RBinsonB/Nox_robot/CAD/Solidworks/Kinect support/wood_planck_kinect.SLDPRT

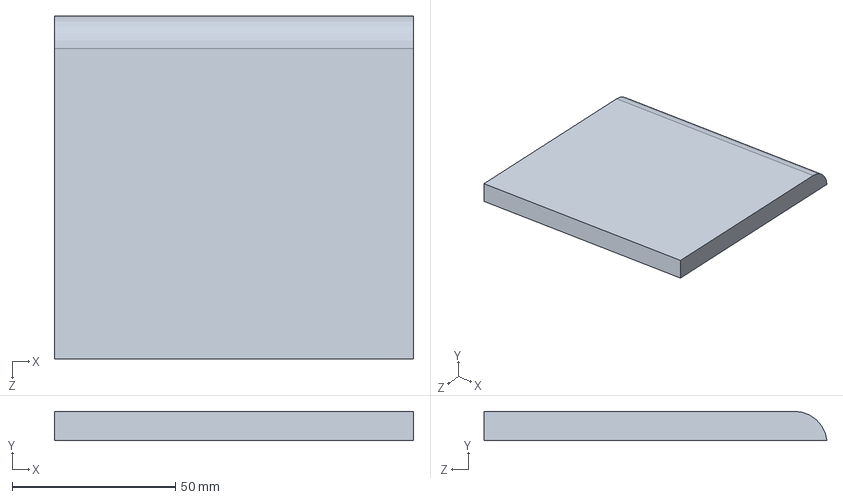
[picture p22: CAD file, 2019-08-14]
CAD/Solidworks/Kinect support/wood_planck_kinect.SLDPRT
110.0 x 9.00 x 105.0 mm
