RBinsonB/Nox_robot/CAD/Solidworks/Motor/Attache_moteur.SLDPRT

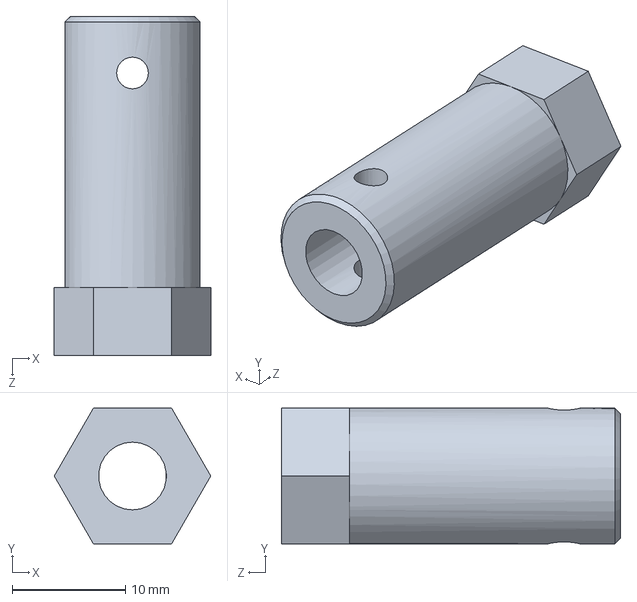
[picture p23: CAD file, 2019-08-14]
CAD/Solidworks/Motor/Attache_moteur.SLDPRT
13.9 x 12.0 x 30.0 mm
