RBinsonB/Nox_robot/CAD/Solidworks/Pivoting roller/Roller.SLDPRT

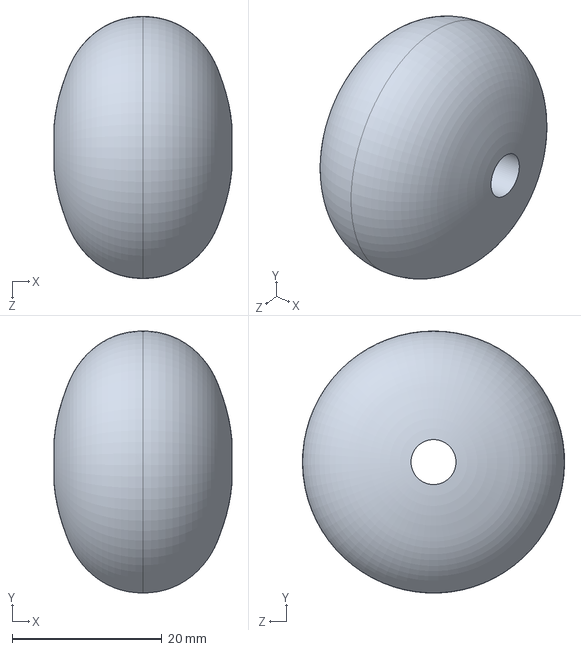
[picture p24: CAD file, 2019-08-14]
CAD/Solidworks/Pivoting roller/Roller.SLDPRT
23.7 x 35.0 x 35.0 mm
