RBinsonB/Nox_robot/CAD/Solidworks/Raspberry Pi Model B 3/rj45 port.SLDPRT

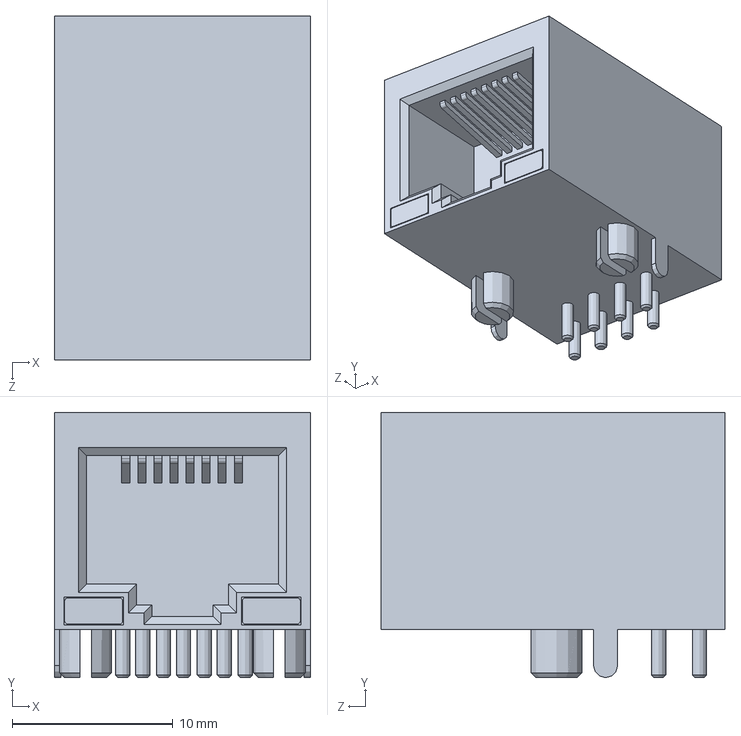
[picture p25: CAD file, 2019-08-14]
CAD/Solidworks/Raspberry Pi Model B 3/rj45 port.SLDPRT
15.9 x 16.5 x 21.4 mm
