RBinsonB/Nox_robot/nox_description/meshes/wheel.STL

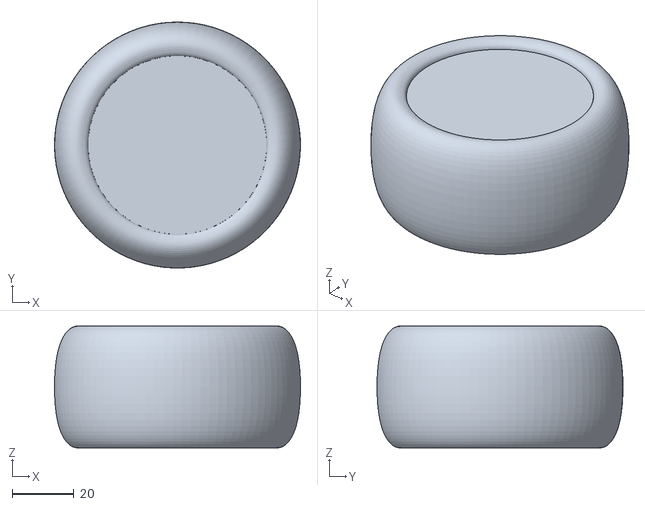
[picture p26: CAD file, 2018-10-01]
nox_description/meshes/wheel.STL
80.0 x 80.0 x 39.6
