RBinsonB/Nox_robot/CAD/Solidworks/Arduino Uno/603 cap on pad.SLDPRT

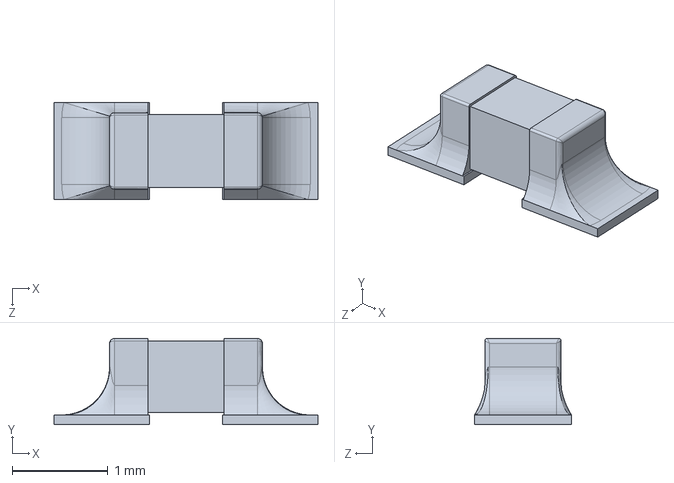
[picture p27: CAD file, 2019-08-14]
CAD/Solidworks/Arduino Uno/603 cap on pad.SLDPRT
2.76 x 0.9 x 1.02 mm
