RBinsonB/Nox_robot/CAD/Solidworks/Carter/Top.sldprt

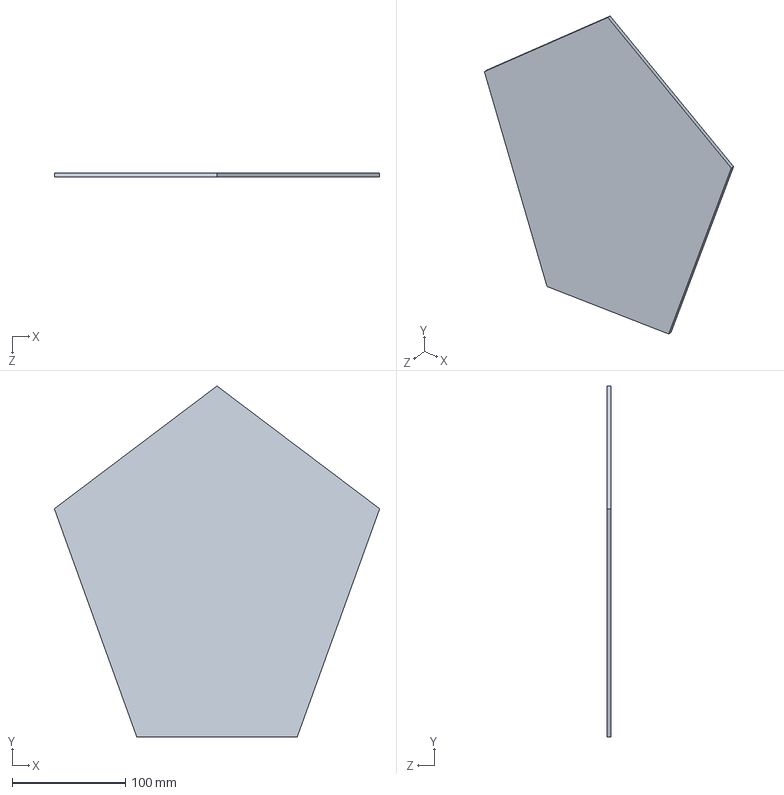
[picture p28: CAD file, 2019-08-14]
CAD/Solidworks/Carter/Top.sldprt
287.4 x 310.0 x 3.50 mm
