RBinsonB/Nox_robot/CAD/Solidworks/Kinect support/wedge_kinect.SLDPRT

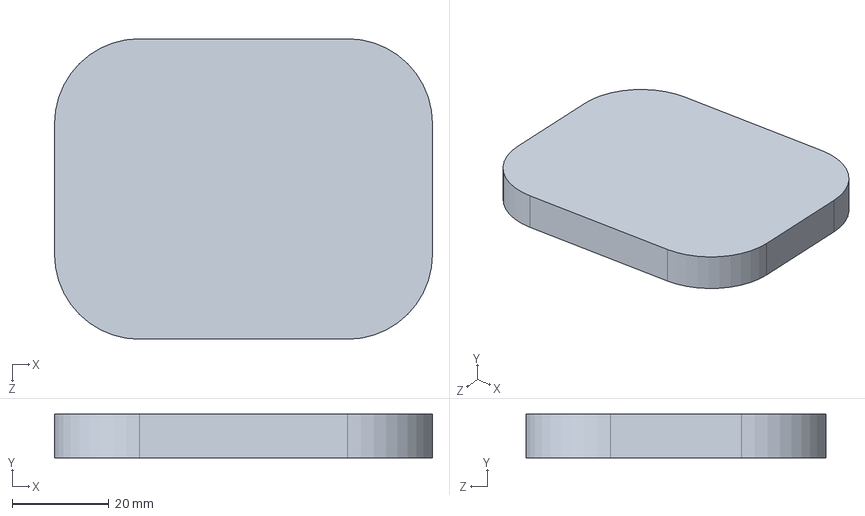
[picture p29: CAD file, 2019-08-14]
CAD/Solidworks/Kinect support/wedge_kinect.SLDPRT
78.0 x 9.00 x 62.0 mm
