RBinsonB/Nox_robot/CAD/Solidworks/Kinect/kinect lens cover.SLDPRT

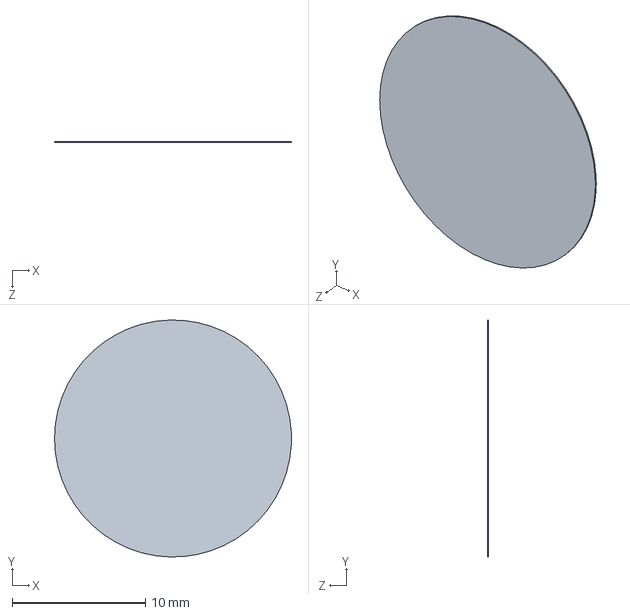
[picture p30: CAD file, 2019-08-14]
CAD/Solidworks/Kinect/kinect lens cover.SLDPRT
17.8 x 17.8 x 0.0992 mm
