RBinsonB/Nox_robot/CAD/Solidworks/Motor/Support.SLDPRT

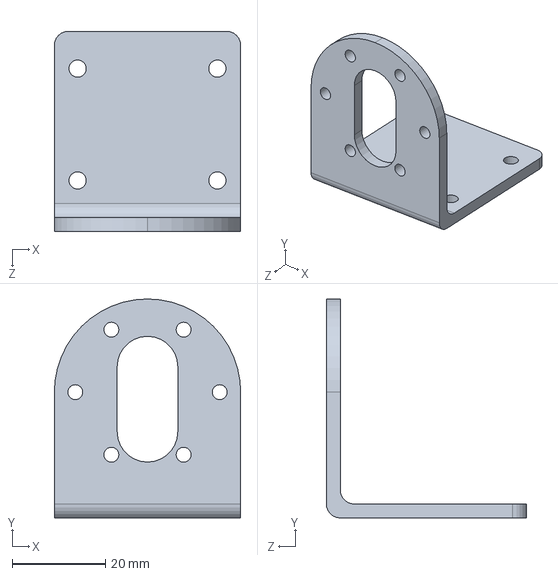
[picture p31: CAD file, 2019-08-14]
CAD/Solidworks/Motor/Support.SLDPRT
40.0 x 47.0 x 43.0 mm
