RBinsonB/Nox_robot/CAD/Solidworks/Raspberry Pi Model B 3/pins.SLDPRT

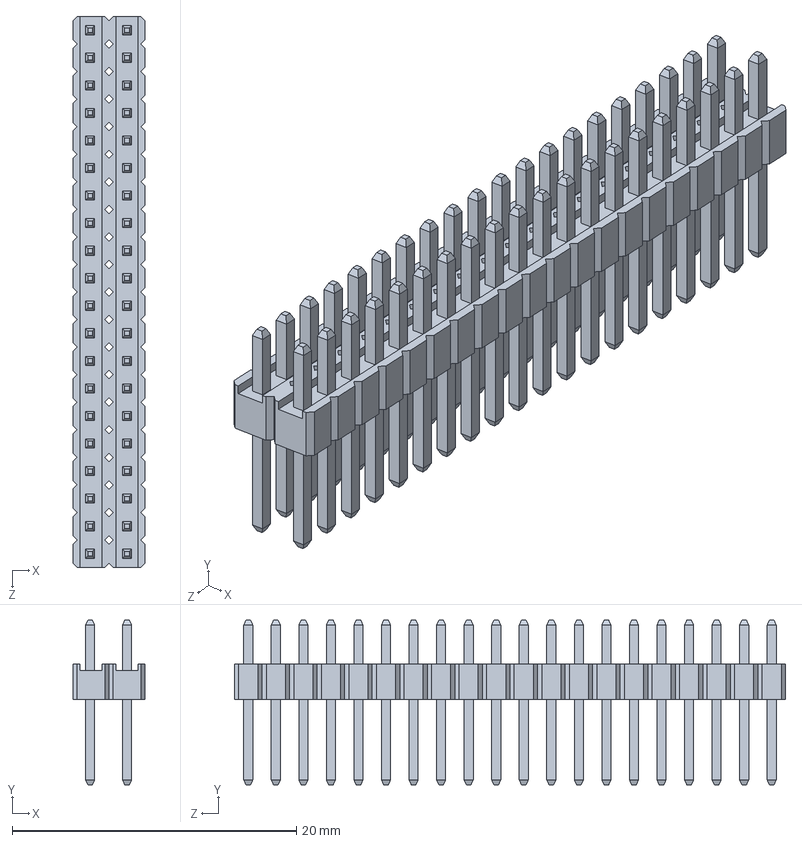
[picture p32: CAD file, 2019-08-14]
CAD/Solidworks/Raspberry Pi Model B 3/pins.SLDPRT
5.08 x 11.6 x 38.8 mm
