RBinsonB/Nox_robot/nox_description/meshes/kinect_sensor.stl

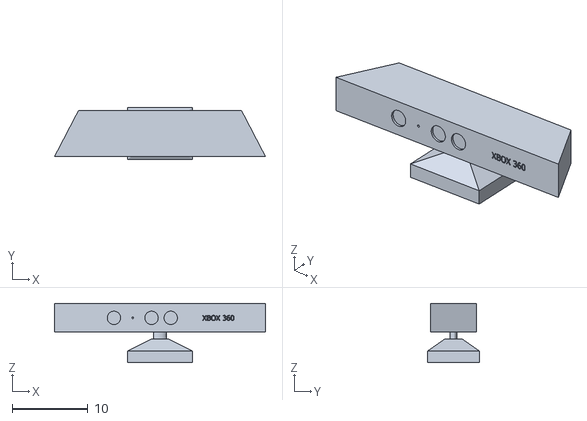
[picture p33: CAD file, 2018-10-01]
nox_description/meshes/kinect_sensor.stl
27.9 x 6.86 x 7.82
