RBinsonB/Nox_robot/CAD/Solidworks/Arduino Uno/220 RESISTOR PACK.SLDPRT

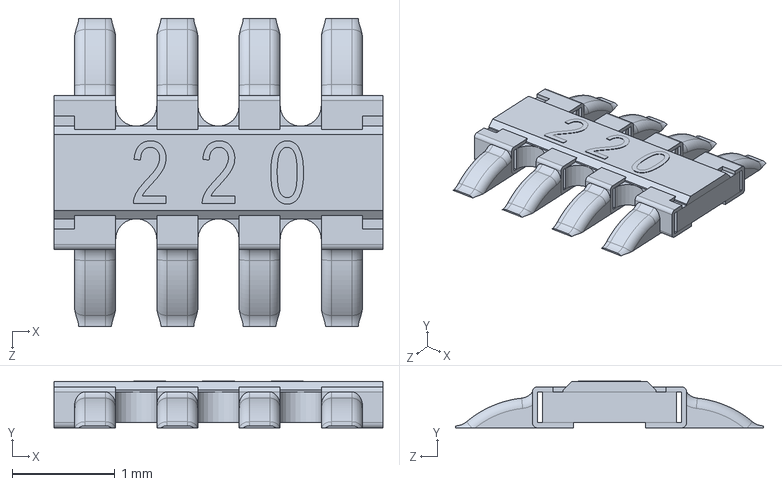
[picture p34: CAD file, 2019-08-14]
CAD/Solidworks/Arduino Uno/220 RESISTOR PACK.SLDPRT
3.20 x 0.455 x 3.00 mm
