RBinsonB/Nox_robot/CAD/Solidworks/Carter/Left_top.sldprt

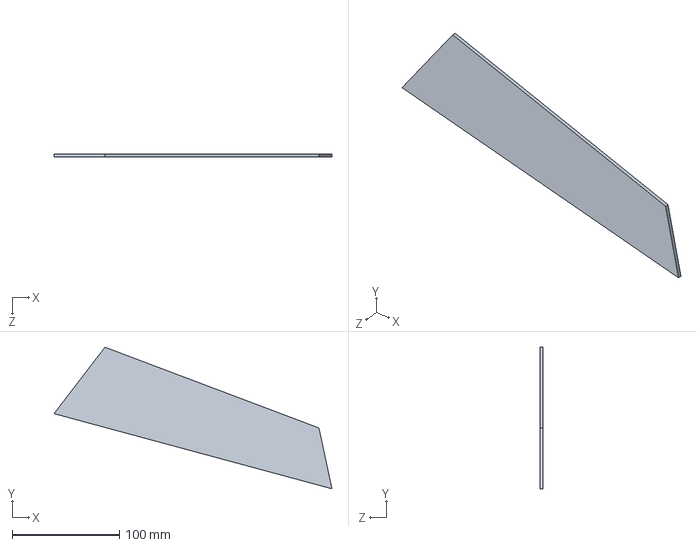
[picture p35: CAD file, 2019-08-14]
CAD/Solidworks/Carter/Left_top.sldprt
259.1 x 132.0 x 3.00 mm
