RBinsonB/Nox_robot/CAD/Solidworks/Kinect support/wood_block.SLDPRT

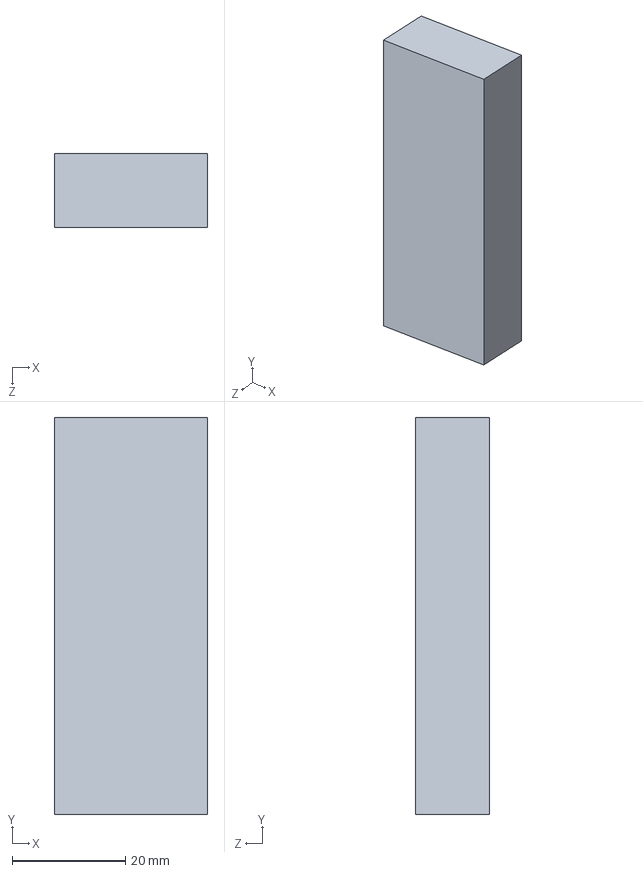
[picture p36: CAD file, 2019-08-14]
CAD/Solidworks/Kinect support/wood_block.SLDPRT
27.0 x 70.0 x 13.0 mm
