RBinsonB/Nox_robot/CAD/Solidworks/Kinect/kinect pivot.SLDPRT

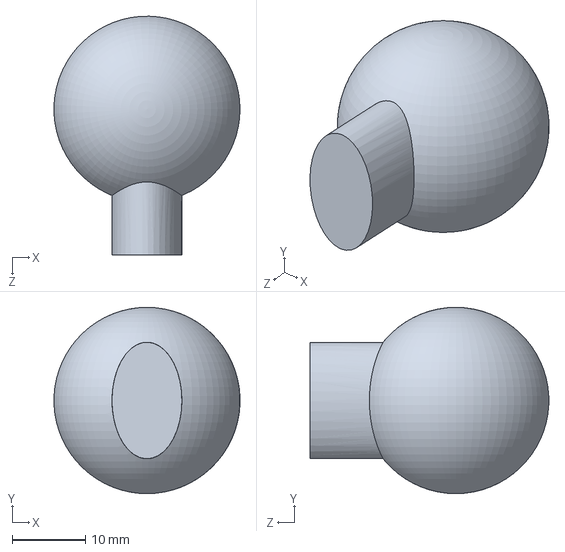
[picture p37: CAD file, 2019-08-14]
CAD/Solidworks/Kinect/kinect pivot.SLDPRT
25.4 x 25.4 x 32.5 mm
