RBinsonB/Nox_robot/CAD/Solidworks/Pivoting roller/Pivot.SLDPRT

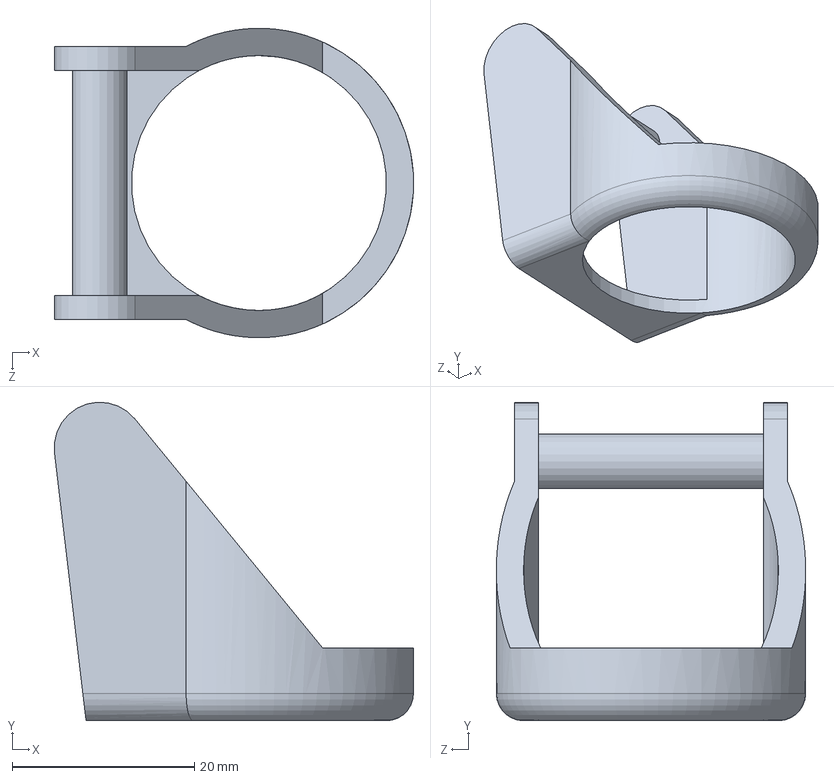
[picture p38: CAD file, 2019-08-14]
CAD/Solidworks/Pivoting roller/Pivot.SLDPRT
39.4 x 35.0 x 34.0 mm
