RBinsonB/Nox_robot/CAD/Solidworks/Roller_wedge.SLDPRT

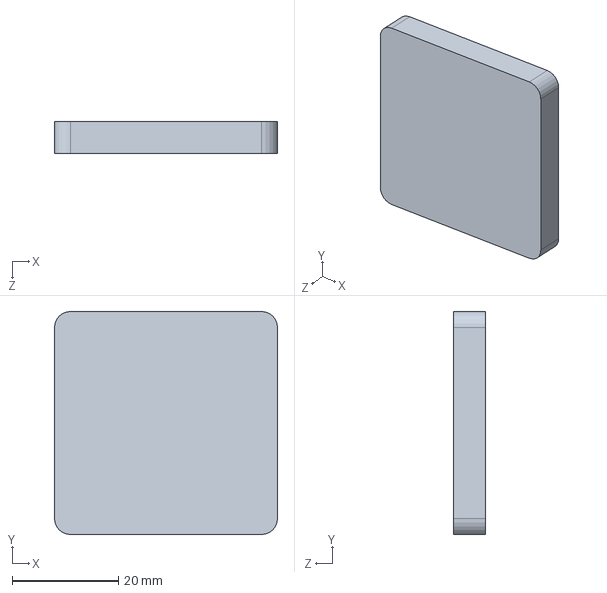
[picture p39: CAD file, 2019-08-14]
CAD/Solidworks/Roller_wedge.SLDPRT
42.0 x 42.0 x 6.00 mm
