RBinsonB/Nox_robot/nox_description/meshes/motor.STL

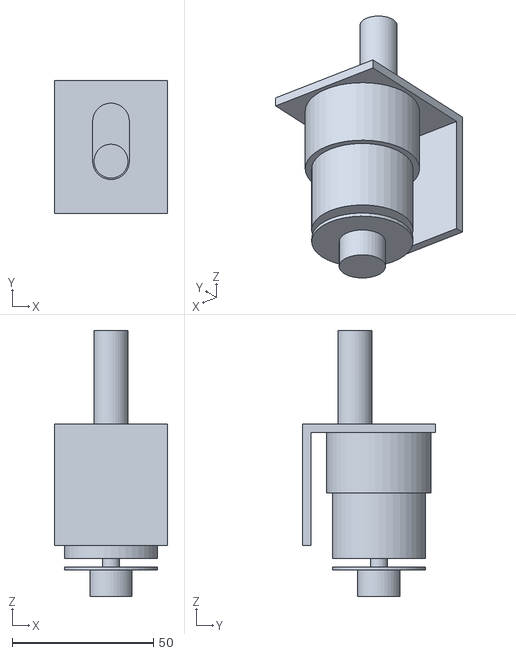
[picture p40: CAD file, 2018-10-01]
nox_description/meshes/motor.STL
40.0 x 47.0 x 94.0
