RBinsonB/Nox_robot/CAD/Solidworks/arduino motor shield.SLDPRT

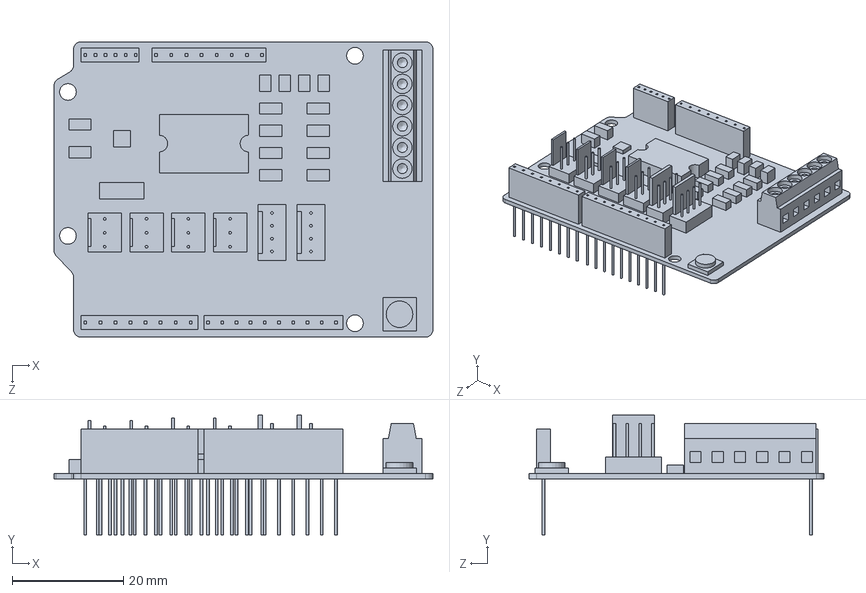
[picture p41: CAD file, 2019-08-14]
CAD/Solidworks/arduino motor shield.SLDPRT
68.0 x 21.5 x 53.0 mm
