RBinsonB/Nox_robot/CAD/Solidworks/Arduino Uno/USB core.SLDPRT

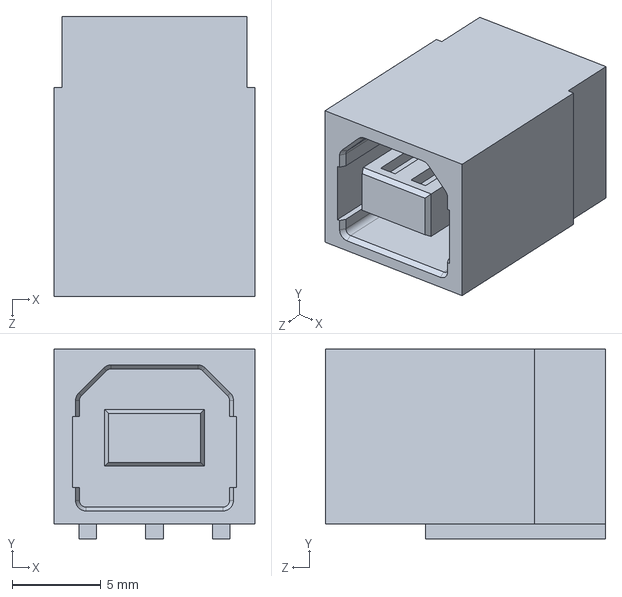
[picture p42: CAD file, 2019-08-14]
CAD/Solidworks/Arduino Uno/USB core.SLDPRT
11.3 x 10.7 x 15.8 mm
