RBinsonB/Nox_robot/CAD/Solidworks/Carter/Rear.sldprt

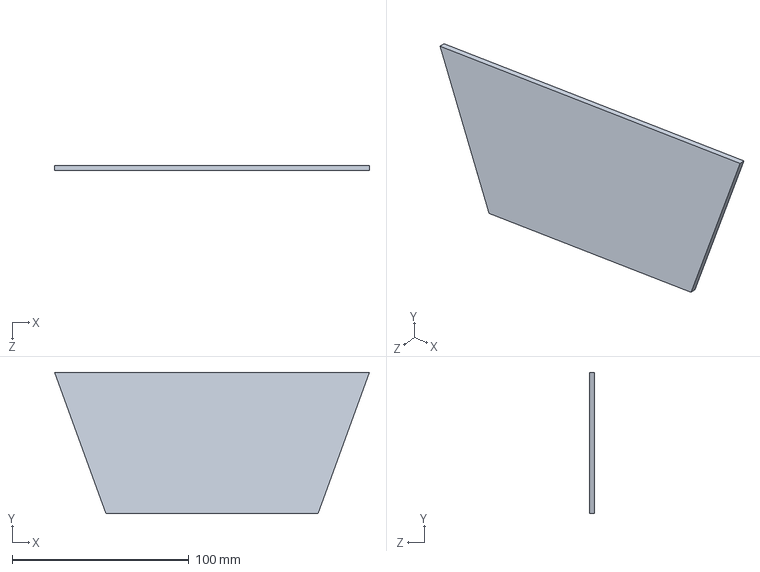
[picture p43: CAD file, 2019-08-14]
CAD/Solidworks/Carter/Rear.sldprt
178.2 x 80.0 x 3.00 mm
