RBinsonB/Nox_robot/CAD/Solidworks/Kinect support/Angle iron right.SLDPRT

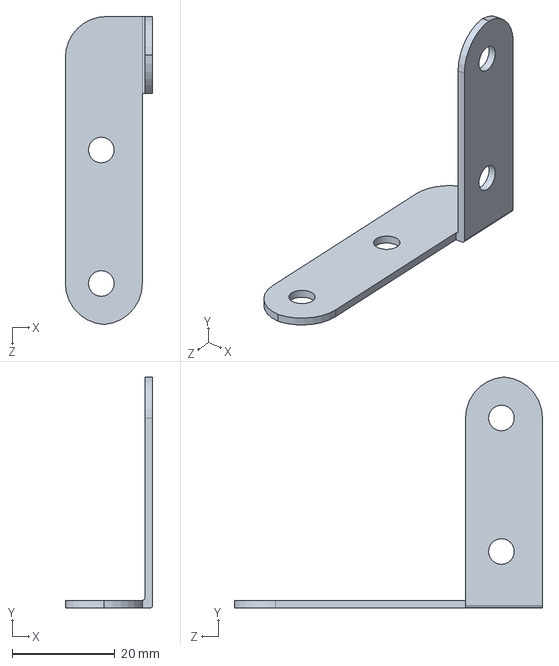
[picture p44: CAD file, 2019-08-14]
CAD/Solidworks/Kinect support/Angle iron right.SLDPRT
17.0 x 45.0 x 60.0 mm
