RBinsonB/Nox_robot/CAD/Solidworks/Kinect/kinect.SLDPRT

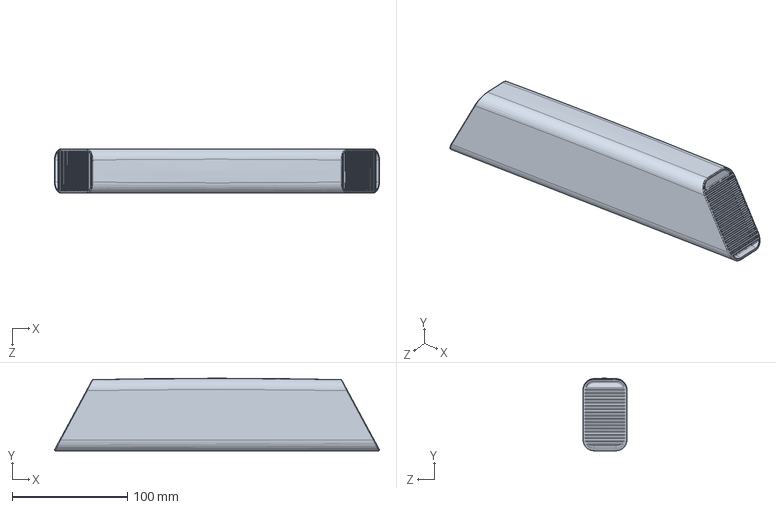
[picture p45: CAD file, 2019-08-14]
CAD/Solidworks/Kinect/kinect.SLDPRT
281.5 x 62.9 x 38.1 mm
