RBinsonB/Nox_robot/CAD/Solidworks/Motor/Pneu.SLDPRT

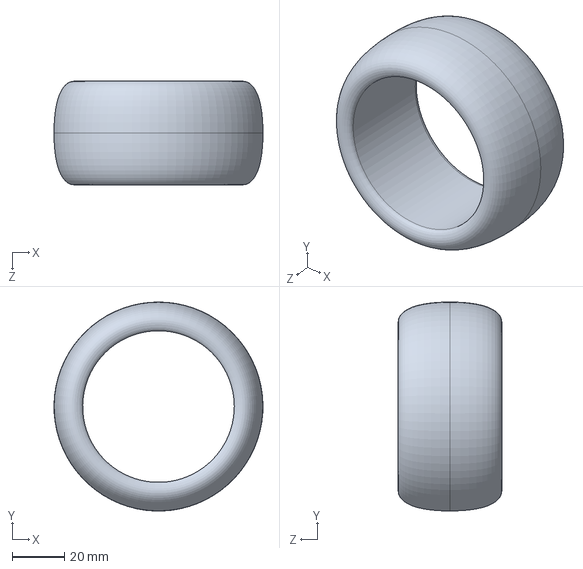
[picture p46: CAD file, 2019-08-14]
CAD/Solidworks/Motor/Pneu.SLDPRT
80.0 x 80.0 x 39.6 mm
