RBinsonB/Nox_robot/CAD/Solidworks/Pivoting roller/roller_base.SLDPRT

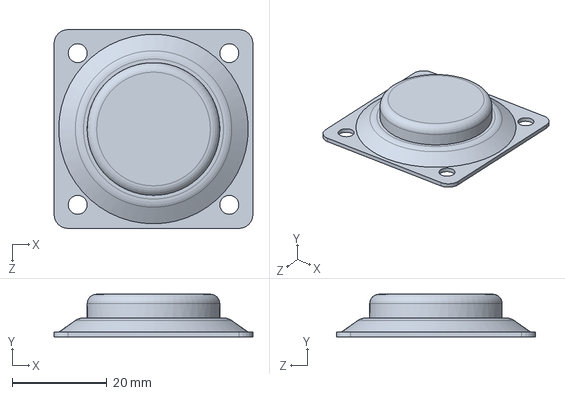
[picture p47: CAD file, 2019-08-14]
CAD/Solidworks/Pivoting roller/roller_base.SLDPRT
42.0 x 9.00 x 42.0 mm
