RBinsonB/Nox_robot/CAD/Solidworks/Raspberry Pi Model B 3/USB port.SLDPRT

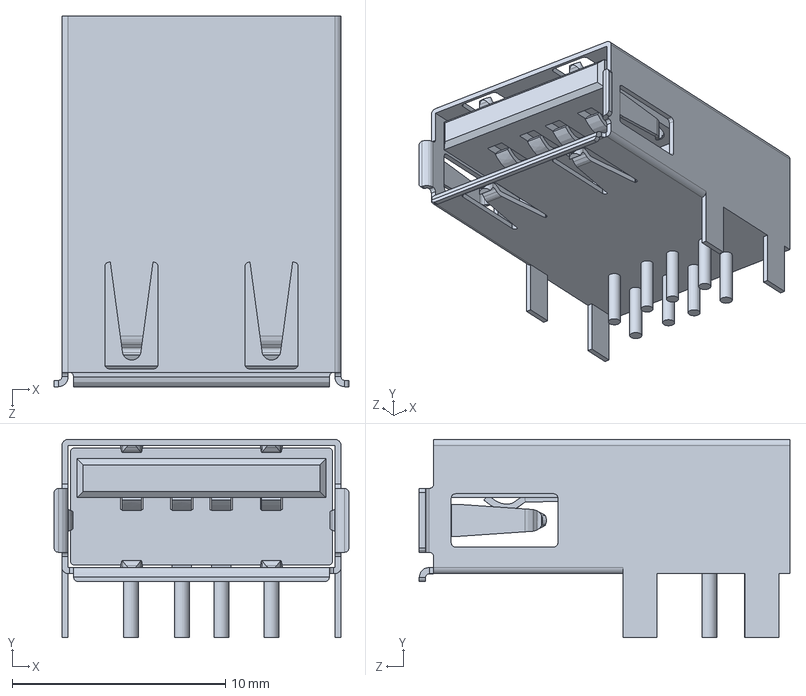
[picture p48: CAD file, 2019-08-14]
CAD/Solidworks/Raspberry Pi Model B 3/USB port.SLDPRT
13.8 x 9.30 x 17.4 mm
