RBinsonB/Nox_robot/nox_description/meshes/base.STL

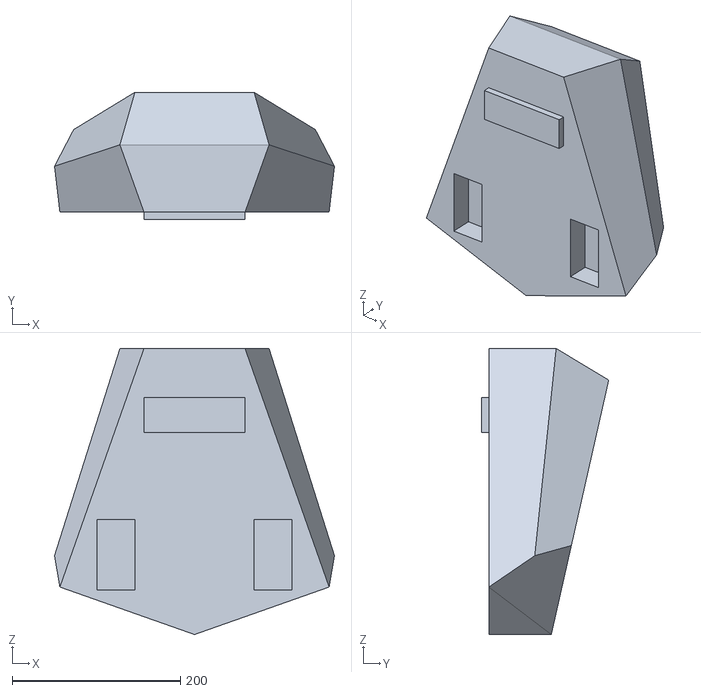
[picture p49: CAD file, 2018-10-01]
nox_description/meshes/base.STL
332.8 x 151.5 x 340.0
