RBinsonB/Nox_robot/CAD/Solidworks/Arduino Uno/cd1206 diode.SLDPRT

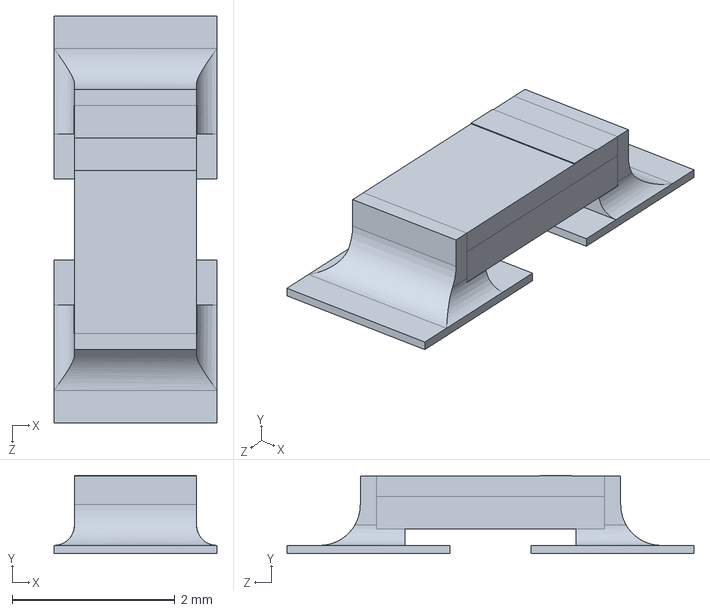
[picture p50: CAD file, 2019-08-14]
CAD/Solidworks/Arduino Uno/cd1206 diode.SLDPRT
2.00 x 0.96 x 5.00 mm
