RBinsonB/Nox_robot/CAD/Solidworks/Carter/Front_left.sldprt

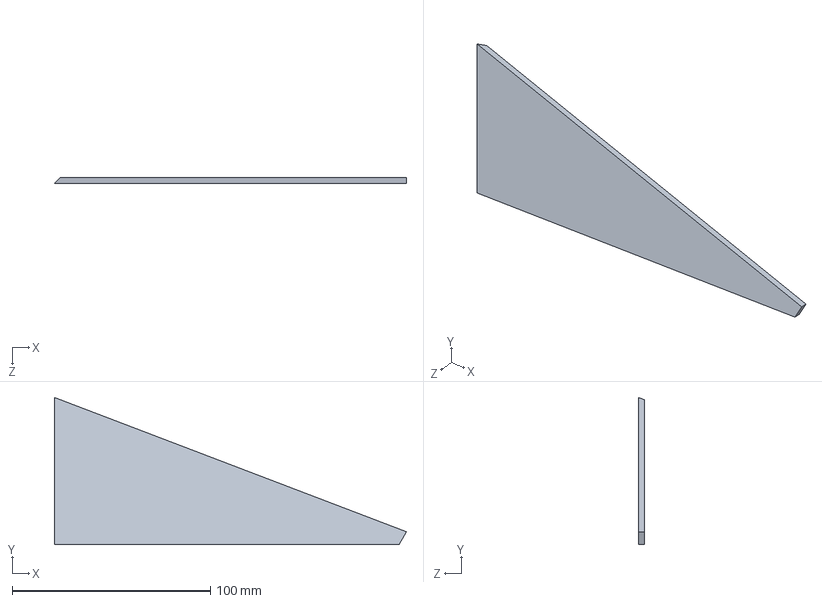
[picture p51: CAD file, 2019-08-14]
CAD/Solidworks/Carter/Front_left.sldprt
177.7 x 74.2 x 3.00 mm
