RBinsonB/Nox_robot/CAD/Solidworks/Kinect support/Angle iron left.SLDPRT

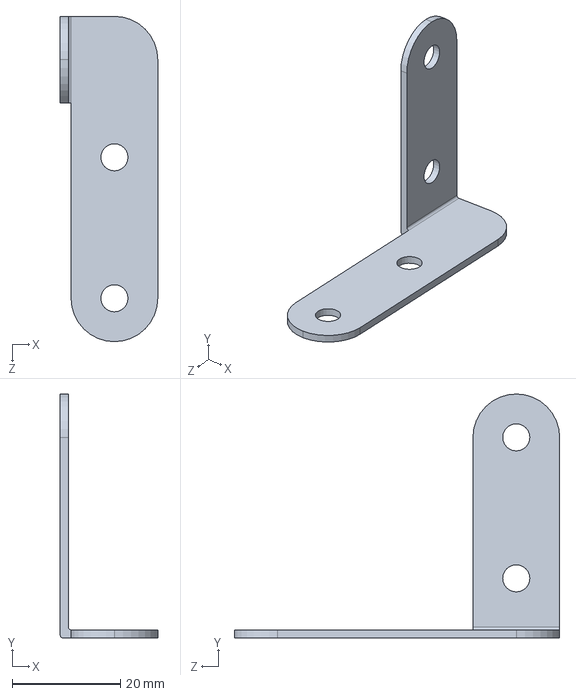
[picture p52: CAD file, 2019-08-14]
CAD/Solidworks/Kinect support/Angle iron left.SLDPRT
18.0 x 45.0 x 60.0 mm
