RBinsonB/Nox_robot/CAD/Solidworks/Kinect/kinect middle lightbulb.SLDPRT

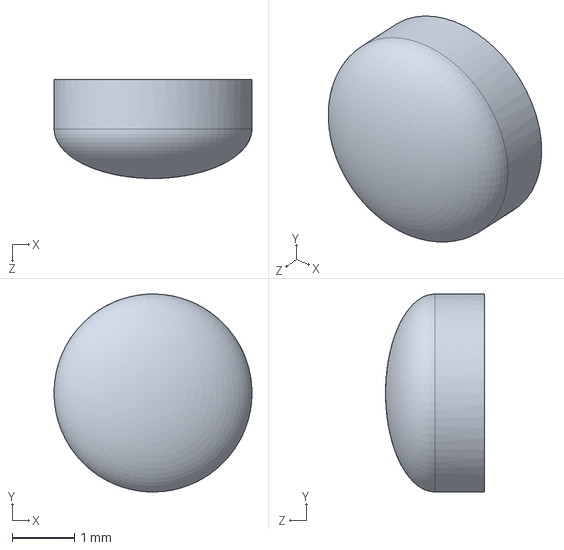
[picture p53: CAD file, 2019-08-14]
CAD/Solidworks/Kinect/kinect middle lightbulb.SLDPRT
3.17 x 3.17 x 1.59 mm
