RBinsonB/Nox_robot/CAD/Solidworks/Motor/Roue.SLDPRT

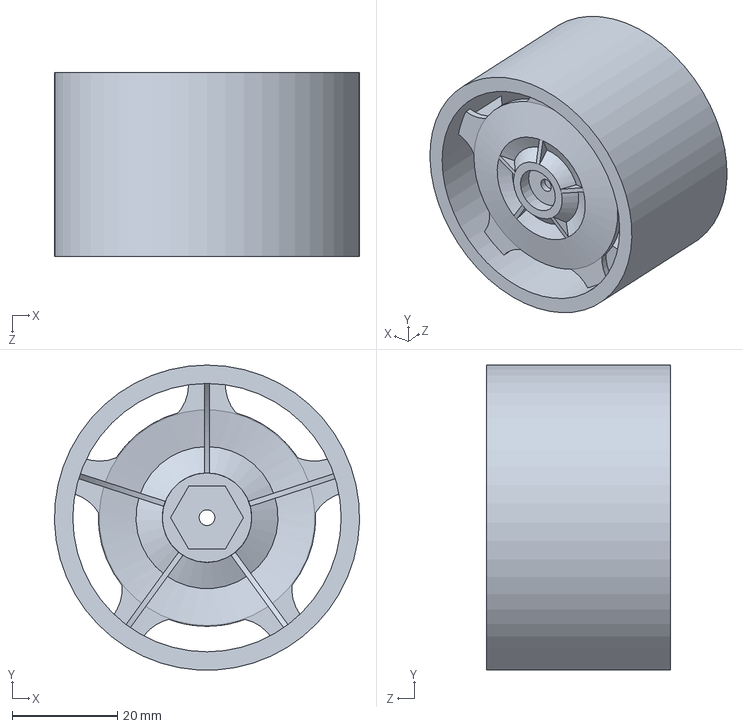
[picture p54: CAD file, 2019-08-14]
CAD/Solidworks/Motor/Roue.SLDPRT
58.0 x 57.9 x 35.0 mm
