RBinsonB/Nox_robot/CAD/Solidworks/Raspberry Pi Model B 3/PCB.SLDPRT

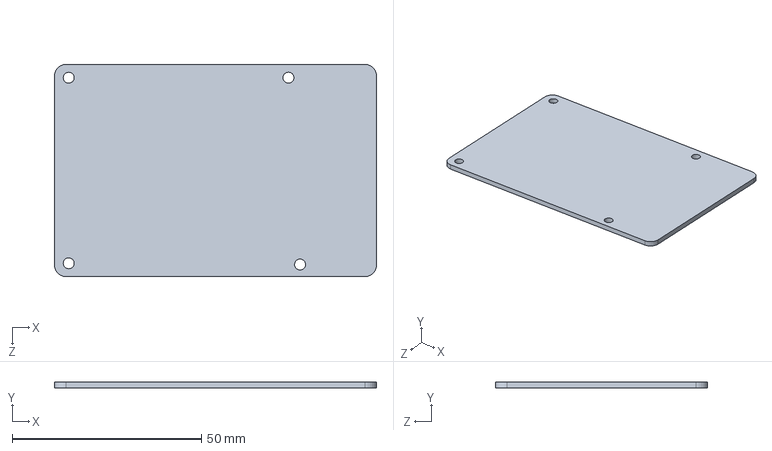
[picture p55: CAD file, 2019-08-14]
CAD/Solidworks/Raspberry Pi Model B 3/PCB.SLDPRT
85.0 x 1.60 x 56.0 mm
