RBinsonB/Nox_robot/nox_description/meshes/support_wheel.STL

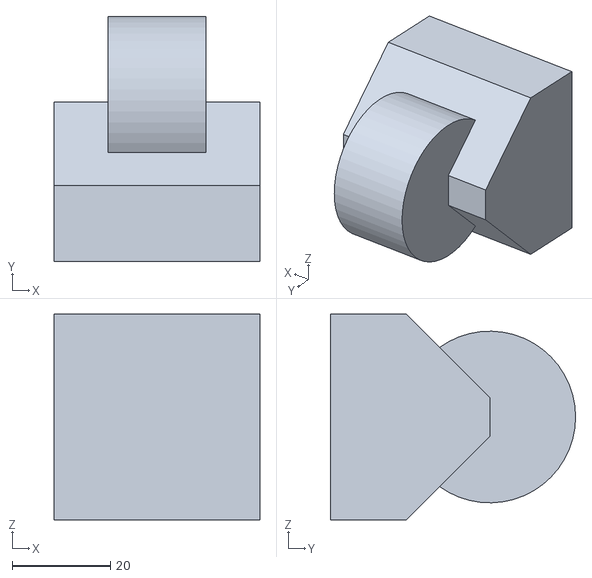
[picture p56: CAD file, 2018-10-01]
nox_description/meshes/support_wheel.STL
42.0 x 50.0 x 42.0
