RBinsonB/Nox_robot/CAD/Solidworks/Arduino Uno/USB SHELL.SLDPRT

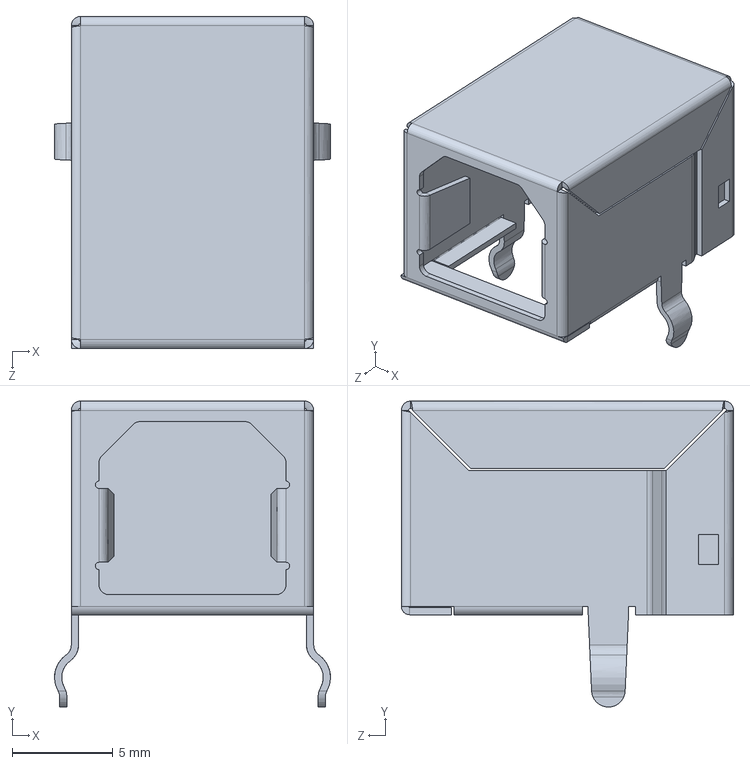
[picture p57: CAD file, 2019-08-14]
CAD/Solidworks/Arduino Uno/USB SHELL.SLDPRT
13.7 x 15.2 x 16.5 mm
