RBinsonB/Nox_robot/CAD/Solidworks/Carter/Front_left_superior.sldprt

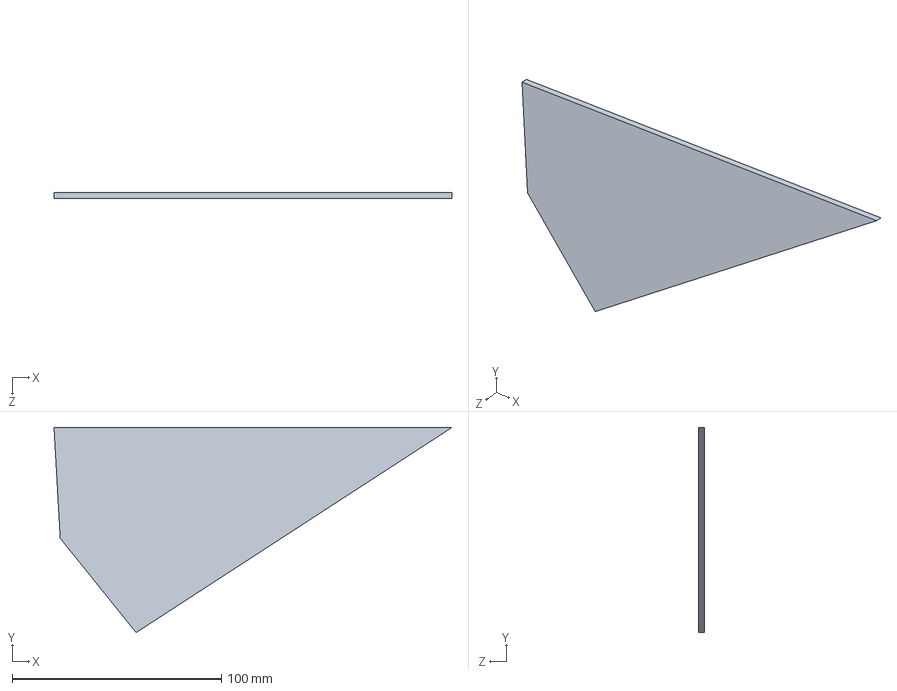
[picture p58: CAD file, 2019-08-14]
CAD/Solidworks/Carter/Front_left_superior.sldprt
190.2 x 98.0 x 3.00 mm
