RBinsonB/Nox_robot/CAD/Solidworks/Kinect/kinect base.SLDPRT

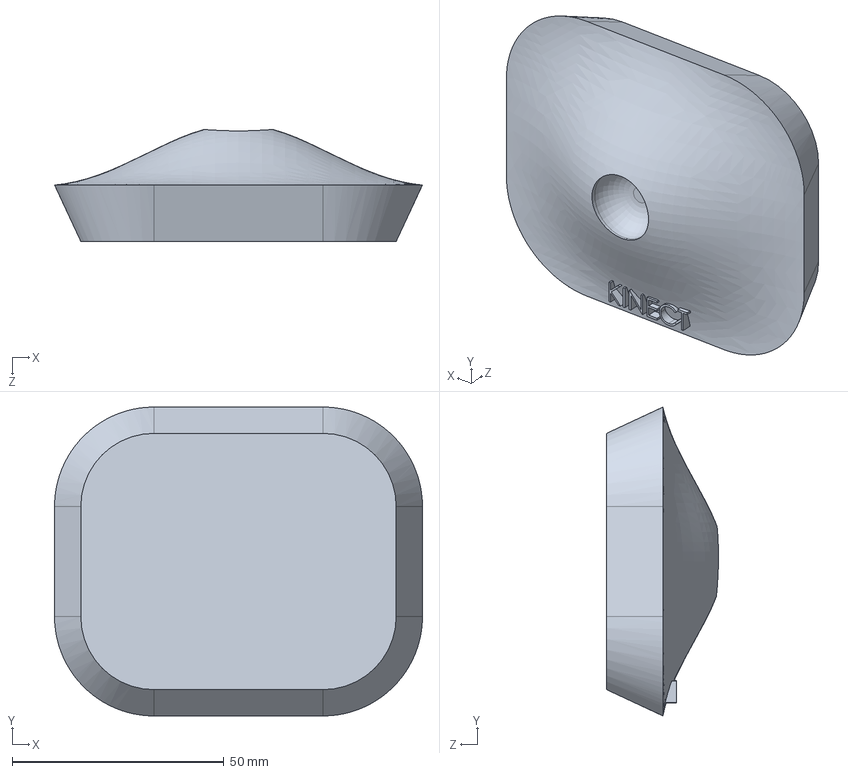
[picture p59: CAD file, 2019-08-14]
CAD/Solidworks/Kinect/kinect base.SLDPRT
87.0 x 73.0 x 26.5 mm
