RBinsonB/Nox_robot/CAD/Solidworks/Motor/Moteur.SLDPRT

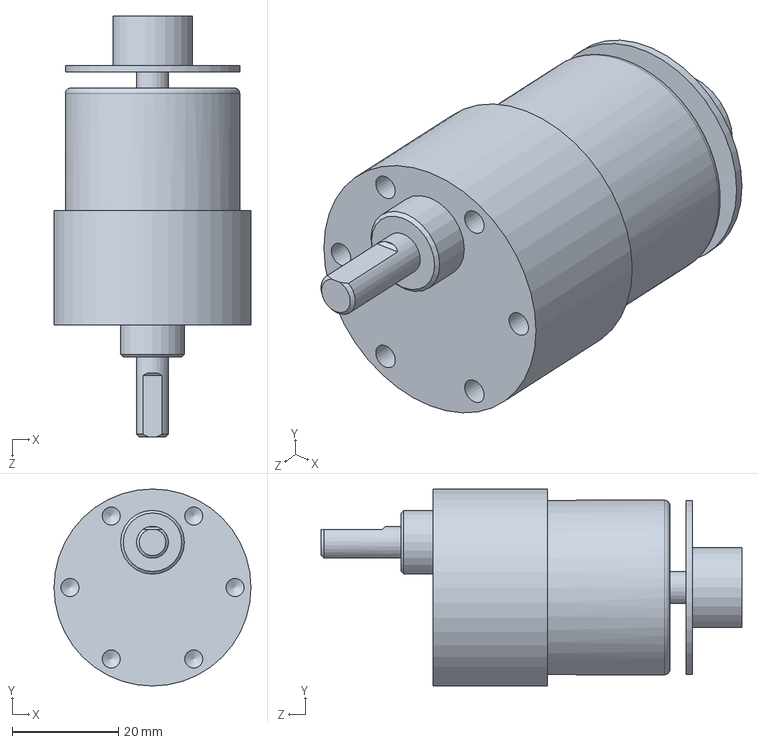
[picture p60: CAD file, 2019-08-14]
CAD/Solidworks/Motor/Moteur.SLDPRT
37.0 x 37.0 x 79.0 mm
