RBinsonB/Nox_robot/CAD/Solidworks/Raspberry Pi Model B 3/ffc lid.SLDPRT

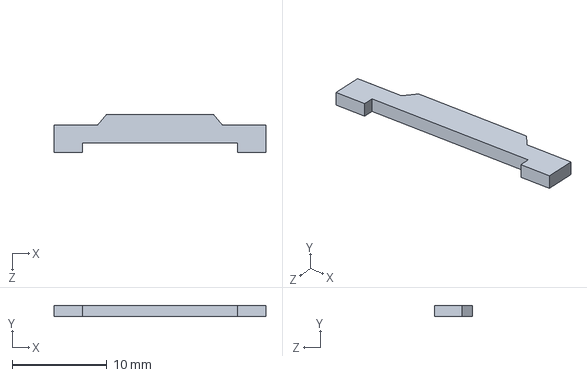
[picture p61: CAD file, 2019-08-14]
CAD/Solidworks/Raspberry Pi Model B 3/ffc lid.SLDPRT
22.4 x 1.20 x 4.01 mm
