RBinsonB/Nox_robot/CAD/Solidworks/Arduino Uno/PADS001.SLDPRT

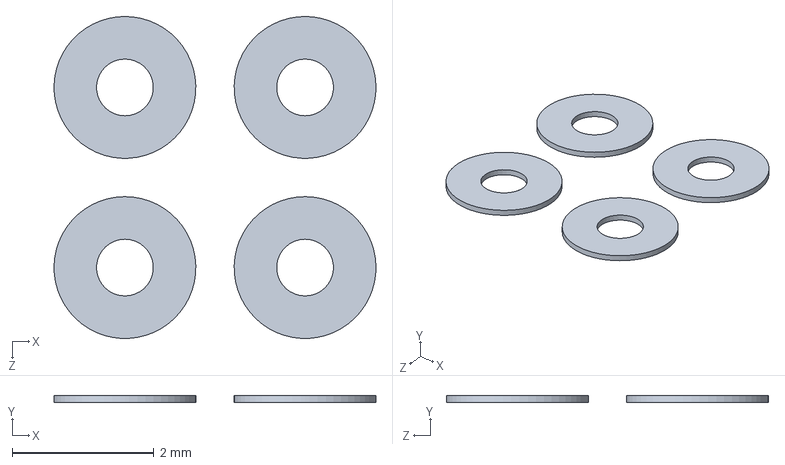
[picture p62: CAD file, 2019-08-14]
CAD/Solidworks/Arduino Uno/PADS001.SLDPRT
4.54 x 0.1 x 4.54 mm
