RBinsonB/Nox_robot/CAD/Solidworks/Carter/Left_bottom.sldprt

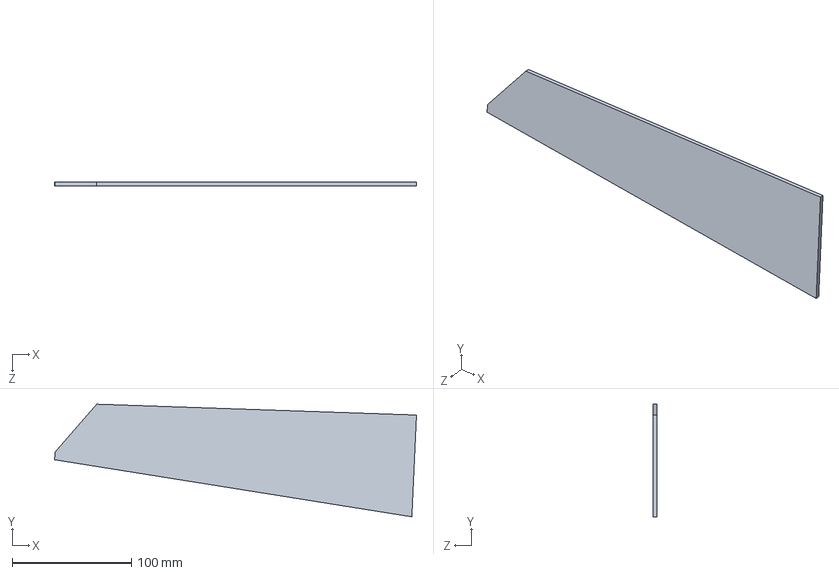
[picture p63: CAD file, 2019-08-14]
CAD/Solidworks/Carter/Left_bottom.sldprt
303.7 x 94.5 x 3.00 mm
