RBinsonB/Nox_robot/CAD/Solidworks/Raspberry Pi Model B 3/audio jack.SLDPRT

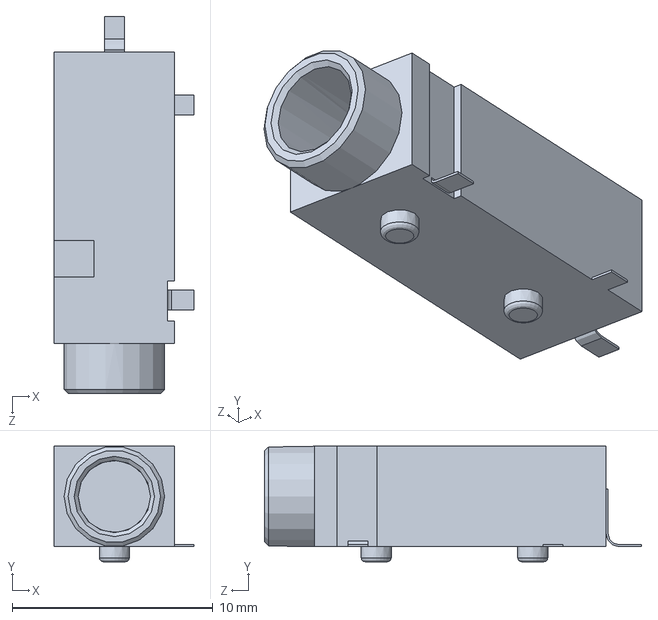
[picture p64: CAD file, 2019-08-14]
CAD/Solidworks/Raspberry Pi Model B 3/audio jack.SLDPRT
6.96 x 5.75 x 18.8 mm
