RBinsonB/Nox_robot/CAD/Solidworks/Arduino Uno/MLC0603.SLDPRT

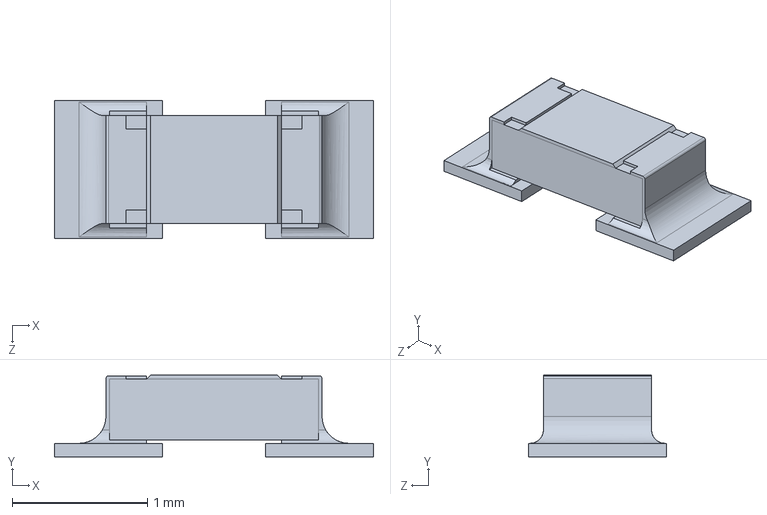
[picture p65: CAD file, 2019-08-14]
CAD/Solidworks/Arduino Uno/MLC0603.SLDPRT
2.36 x 0.605 x 1.02 mm
