RBinsonB/Nox_robot/CAD/Solidworks/Mounting_bracket_long.SLDPRT

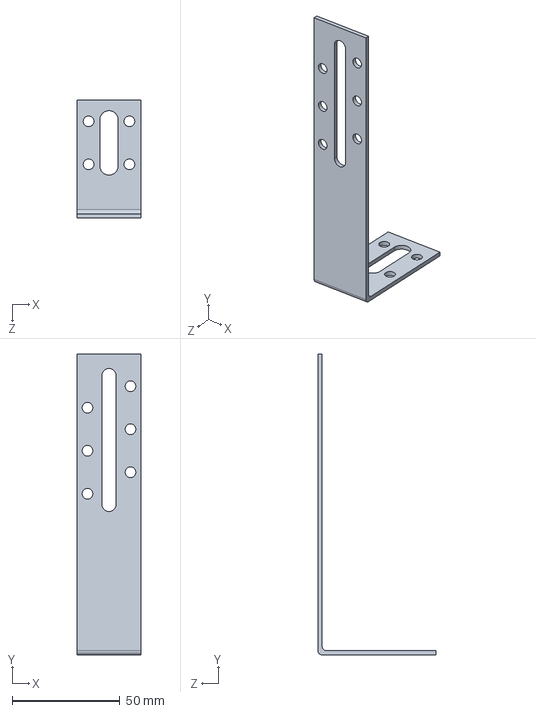
[picture p66: CAD file, 2019-08-14]
CAD/Solidworks/Mounting_bracket_long.SLDPRT
30.0 x 140.0 x 55.0 mm
