RBinsonB/Nox_robot/CAD/Solidworks/Arduino Uno/blm21.SLDPRT

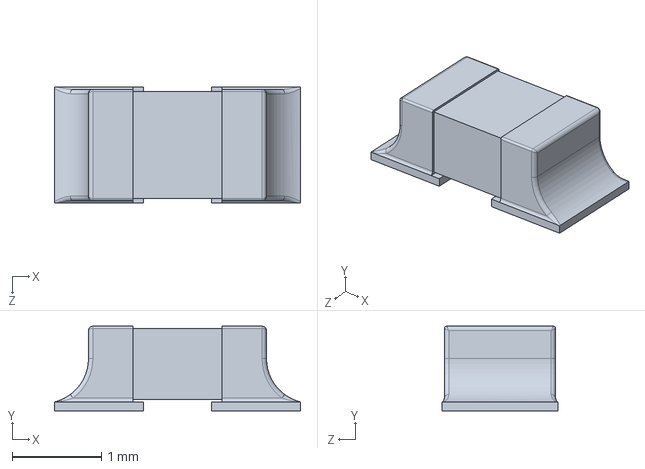
[picture p67: CAD file, 2019-08-14]
CAD/Solidworks/Arduino Uno/blm21.SLDPRT
2.76 x 0.95 x 1.30 mm
