RBinsonB/Nox_robot/CAD/Solidworks/Arduino Uno/usb btm contact.SLDPRT

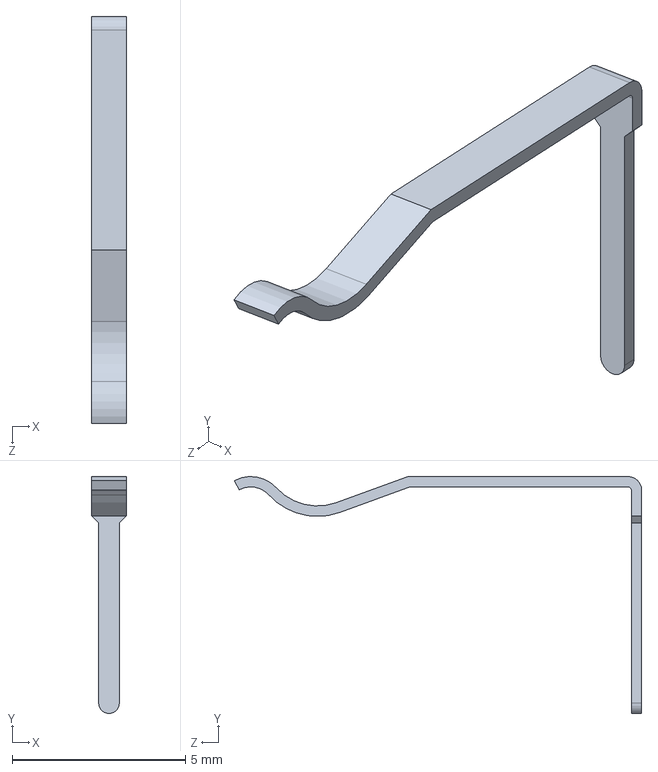
[picture p68: CAD file, 2019-08-14]
CAD/Solidworks/Arduino Uno/usb btm contact.SLDPRT
1.00 x 6.84 x 11.8 mm
