RBinsonB/Nox_robot/CAD/Solidworks/Raspberry Pi Model B 3/mini hdmi.SLDPRT

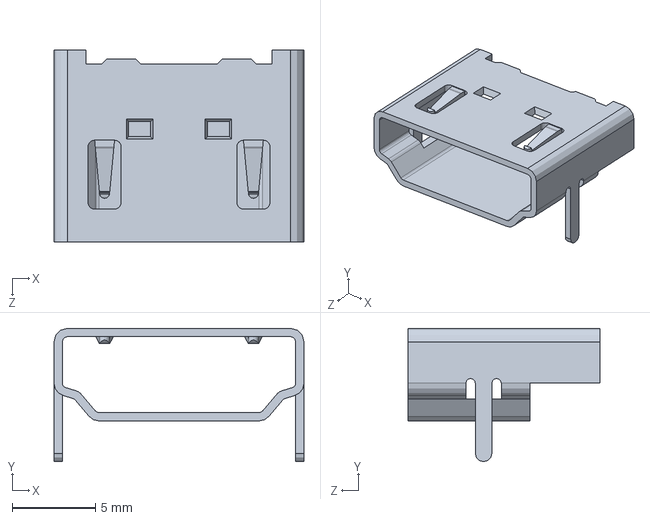
[picture p69: CAD file, 2019-08-14]
CAD/Solidworks/Raspberry Pi Model B 3/mini hdmi.SLDPRT
15.0 x 8.01 x 11.6 mm
