RBinsonB/Nox_robot/CAD/Solidworks/Arduino Uno/6 PORT HEADER.SLDPRT

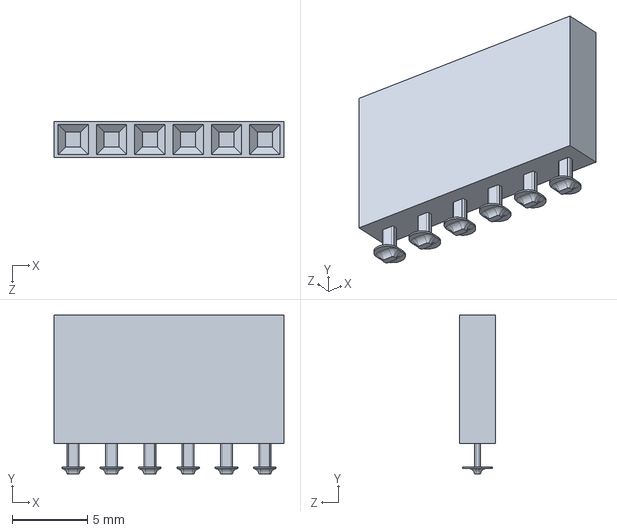
[picture p70: CAD file, 2019-08-14]
CAD/Solidworks/Arduino Uno/6 PORT HEADER.SLDPRT
15.2 x 10.5 x 2.41 mm
