RBinsonB/Nox_robot/CAD/Solidworks/Raspberry Pi Model B 3/15pin FFC.SLDPRT

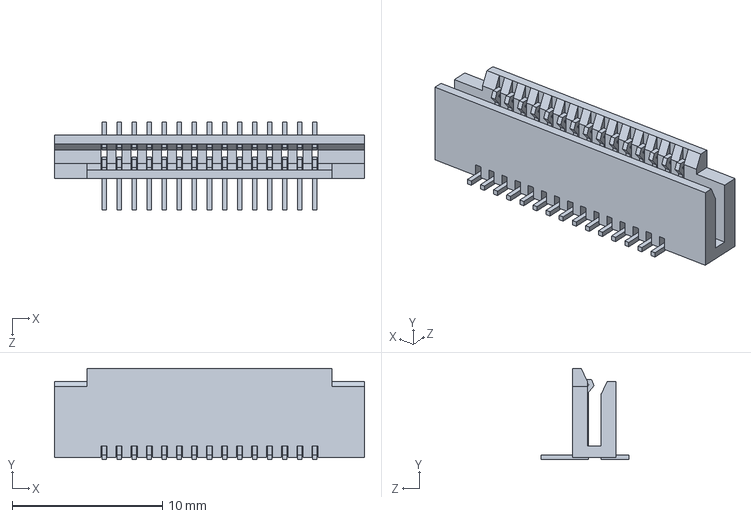
[picture p71: CAD file, 2019-08-14]
CAD/Solidworks/Raspberry Pi Model B 3/15pin FFC.SLDPRT
20.6 x 6.05 x 5.86 mm
