RBinsonB/Nox_robot/CAD/Solidworks/Battery_11v.SLDPRT

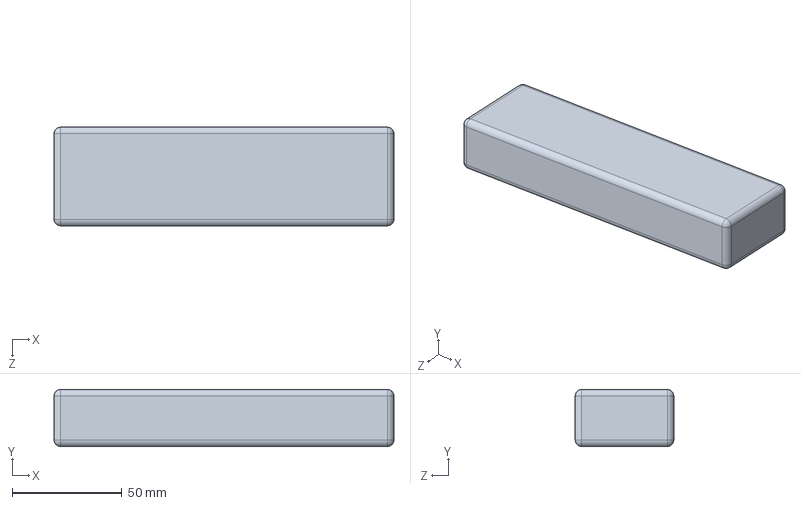
[picture p72: CAD file, 2019-08-14]
CAD/Solidworks/Battery_11v.SLDPRT
155.0 x 26.0 x 45.0 mm
