RBinsonB/Nox_robot/CAD/Solidworks/Arduino Uno/10 PORT HEADER.SLDPRT

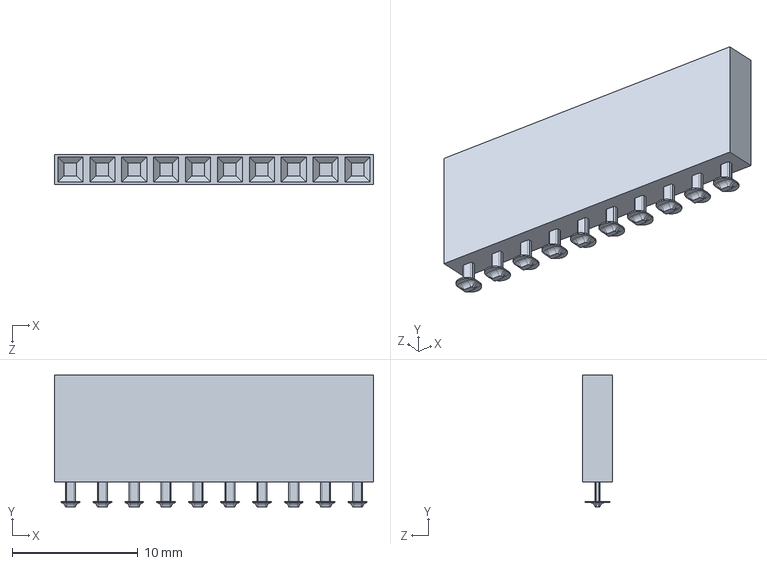
[picture p73: CAD file, 2019-08-14]
CAD/Solidworks/Arduino Uno/10 PORT HEADER.SLDPRT
25.4 x 10.5 x 2.41 mm
