RBinsonB/Nox_robot/CAD/Solidworks/Arduino Uno/dip socket pin.SLDPRT

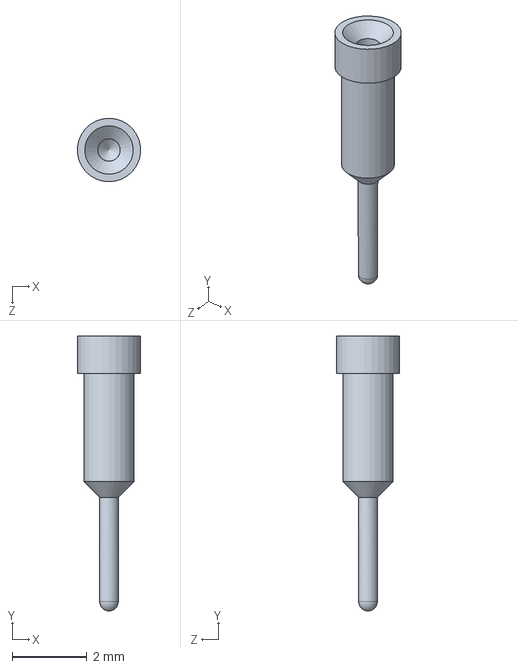
[picture p74: CAD file, 2019-08-14]
CAD/Solidworks/Arduino Uno/dip socket pin.SLDPRT
1.69 x 7.37 x 1.70 mm
