RBinsonB/Nox_robot/CAD/Solidworks/Arduino Uno/unoboard blue.SLDPRT

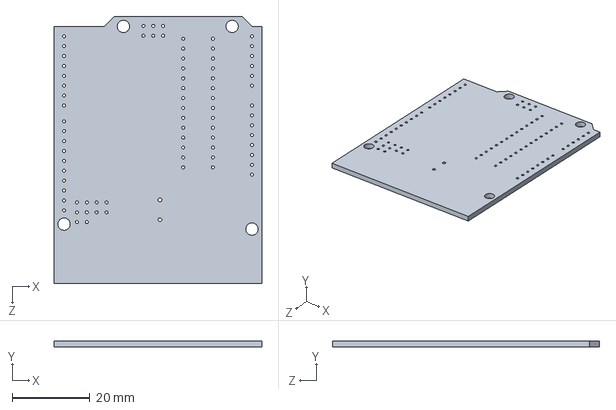
[picture p75: CAD file, 2019-08-14]
CAD/Solidworks/Arduino Uno/unoboard blue.SLDPRT
53.3 x 1.65 x 68.6 mm
