RBinsonB/Nox_robot/CAD/Solidworks/Mounting_bracket_small.SLDPRT

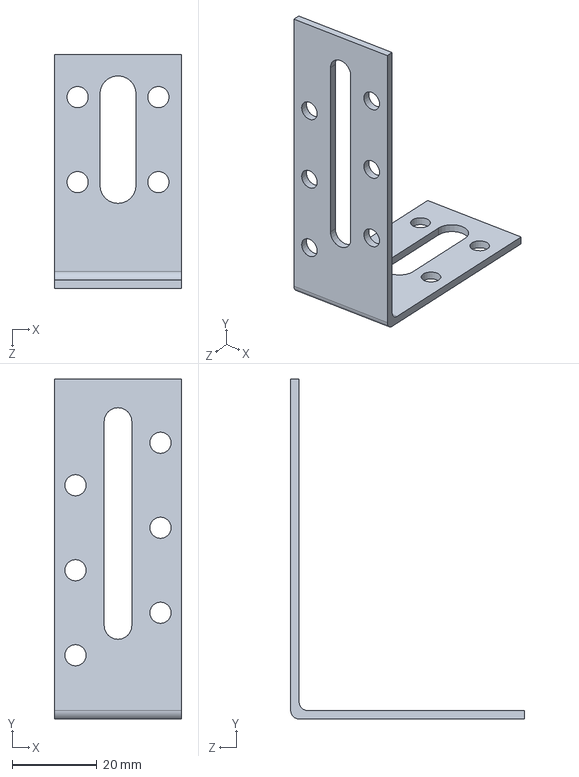
[picture p76: CAD file, 2019-08-14]
CAD/Solidworks/Mounting_bracket_small.SLDPRT
30.0 x 80.0 x 55.0 mm
