RBinsonB/Nox_robot/CAD/Solidworks/Angle small 30.SLDPRT

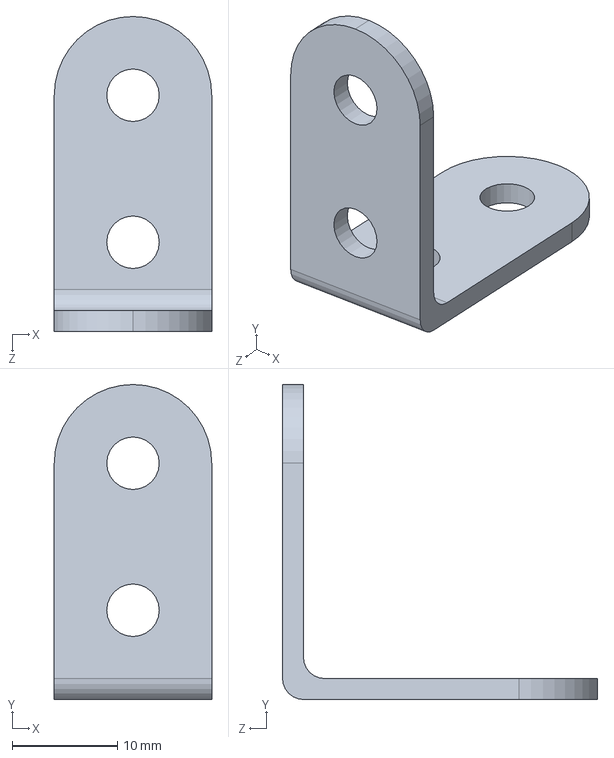
[picture p77: CAD file, 2019-08-14]
CAD/Solidworks/Angle small 30.SLDPRT
15.0 x 30.0 x 30.0 mm
