RBinsonB/Nox_robot/CAD/Solidworks/Arduino Uno/RESET.SLDPRT

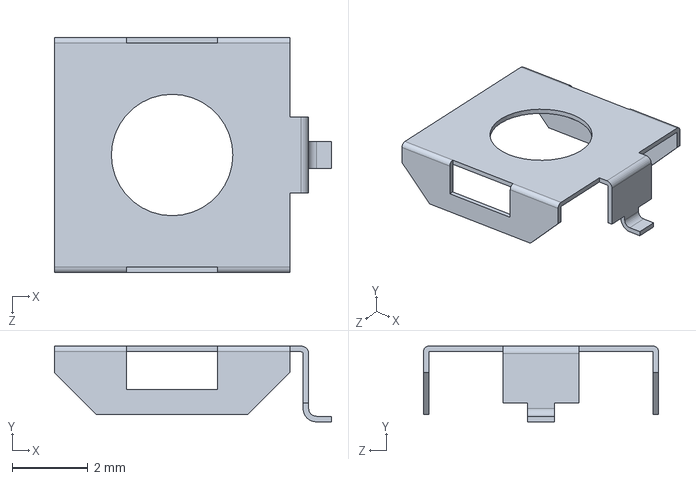
[picture p78: CAD file, 2019-08-14]
CAD/Solidworks/Arduino Uno/RESET.SLDPRT
7.30 x 2.00 x 6.20 mm
