RBinsonB/Nox_robot/CAD/Solidworks/Arduino Uno/ssot3.SLDPRT

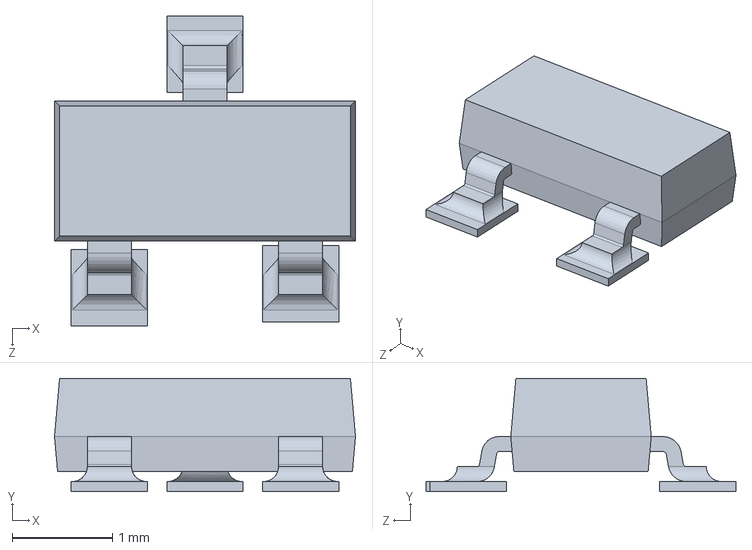
[picture p79: CAD file, 2019-08-14]
CAD/Solidworks/Arduino Uno/ssot3.SLDPRT
3.00 x 1.13 x 3.09 mm
