RBinsonB/Nox_robot/CAD/Solidworks/rear_support.sldprt

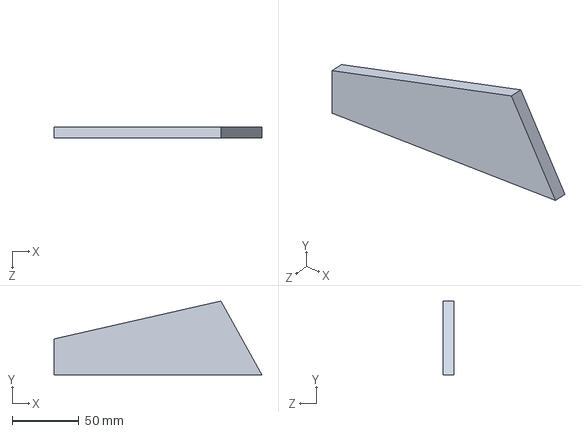
[picture p80: CAD file, 2019-08-14]
CAD/Solidworks/rear_support.sldprt
156.0 x 55.4 x 8.50 mm
