RBinsonB/Nox_robot/CAD/Solidworks/Arduino Uno/nano - reg.SLDPRT

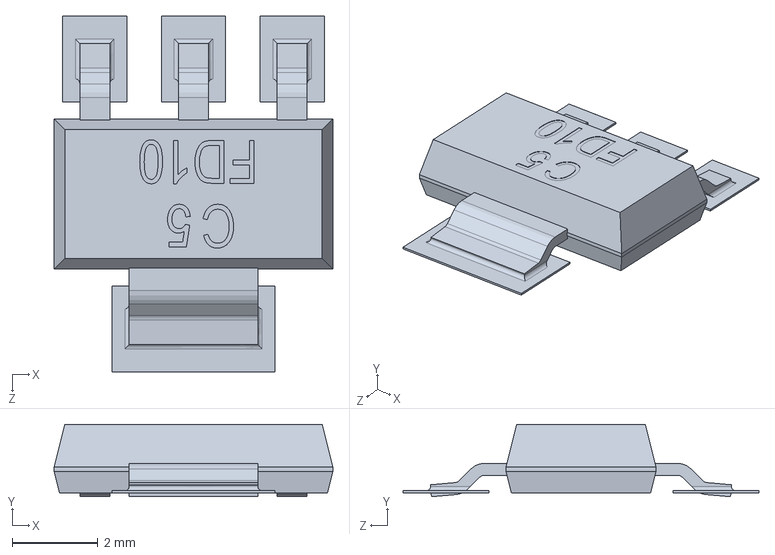
[picture p81: CAD file, 2019-08-14]
CAD/Solidworks/Arduino Uno/nano - reg.SLDPRT
6.50 x 1.69 x 8.30 mm
