RBinsonB/Nox_robot/CAD/Solidworks/Arduino Uno/RESET CORE.SLDPRT

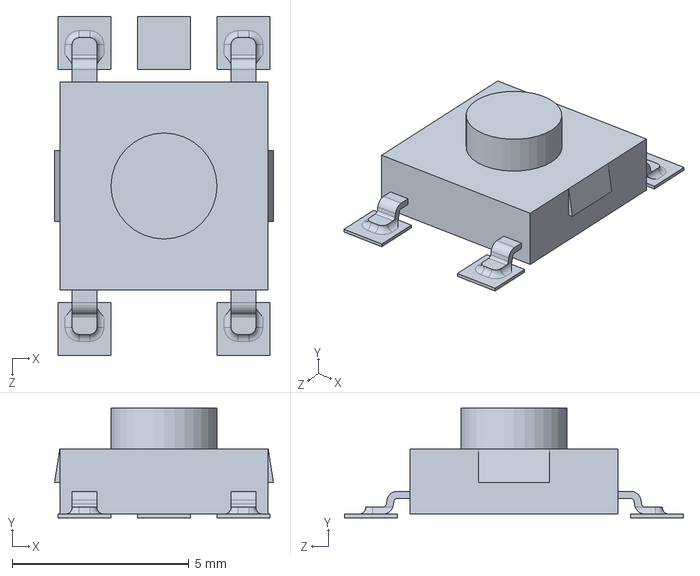
[picture p82: CAD file, 2019-08-14]
CAD/Solidworks/Arduino Uno/RESET CORE.SLDPRT
6.20 x 3.10 x 9.60 mm
