RBinsonB/Nox_robot/CAD/Solidworks/Mounting_bracket.SLDPRT

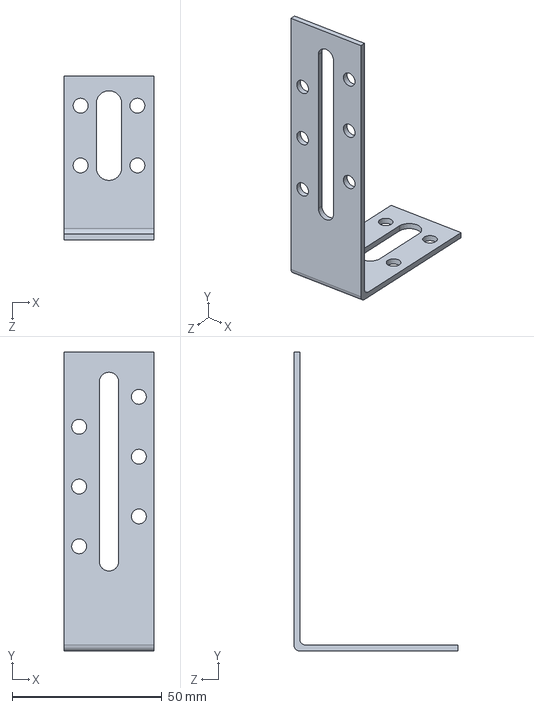
[picture p83: CAD file, 2019-08-14]
CAD/Solidworks/Mounting_bracket.SLDPRT
30.0 x 100.0 x 55.0 mm
