RBinsonB/Nox_robot/CAD/Solidworks/Angle small 50.SLDPRT

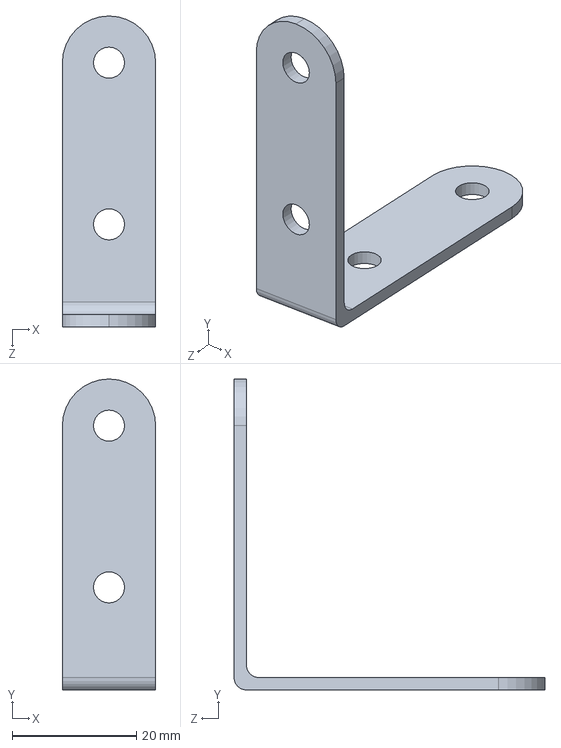
[picture p84: CAD file, 2019-08-14]
CAD/Solidworks/Angle small 50.SLDPRT
15.0 x 50.0 x 50.0 mm
