RBinsonB/Nox_robot/CAD/Solidworks/Arduino Uno/power jack.SLDPRT

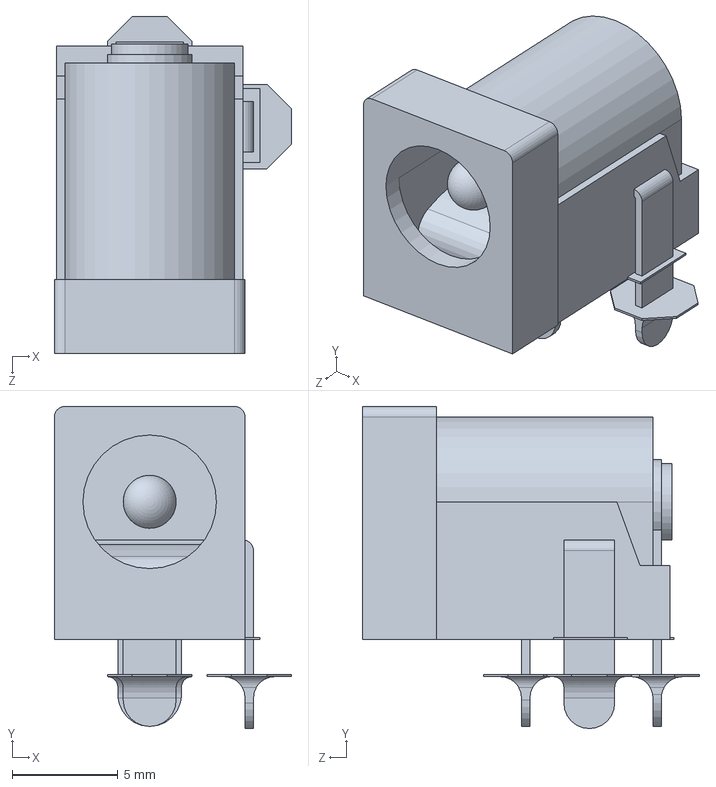
[picture p85: CAD file, 2019-08-14]
CAD/Solidworks/Arduino Uno/power jack.SLDPRT
11.2 x 15.2 x 15.9 mm
