RBinsonB/Nox_robot/CAD/Solidworks/base.SLDPRT

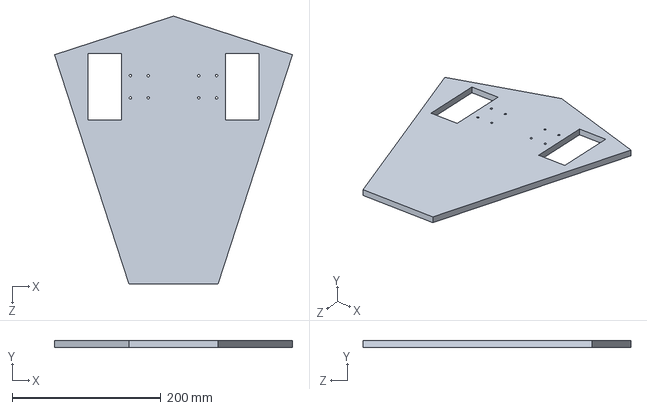
[picture p86: CAD file, 2019-08-14]
CAD/Solidworks/base.SLDPRT
320.0 x 9.00 x 360.0 mm
