RBinsonB/Nox_robot/CAD/Solidworks/Arduino Uno/16mhz crystal - measured.SLDPRT

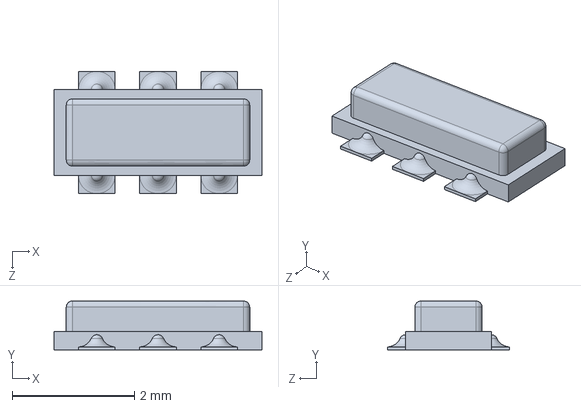
[picture p87: CAD file, 2019-08-14]
CAD/Solidworks/Arduino Uno/16mhz crystal - measured.SLDPRT
3.40 x 0.8 x 2.00 mm
