RBinsonB/Nox_robot/CAD/Solidworks/Electronic support.SLDPRT

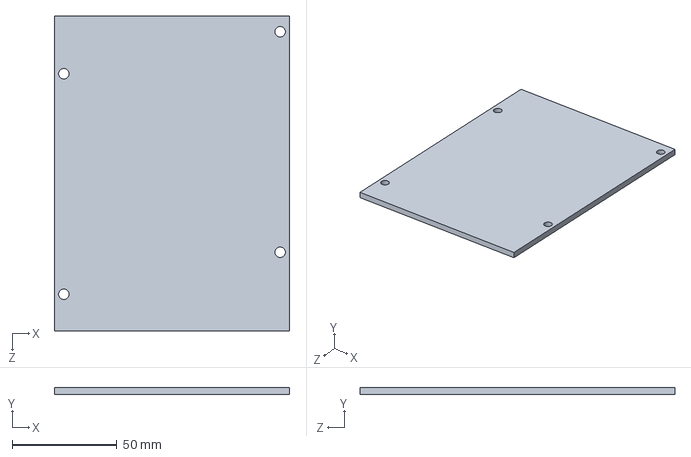
[picture p88: CAD file, 2019-08-14]
CAD/Solidworks/Electronic support.SLDPRT
112.0 x 3.50 x 150.0 mm
