RBinsonB/Nox_robot/CAD/Solidworks/Arduino Uno/mf-msmf050-2.SLDPRT

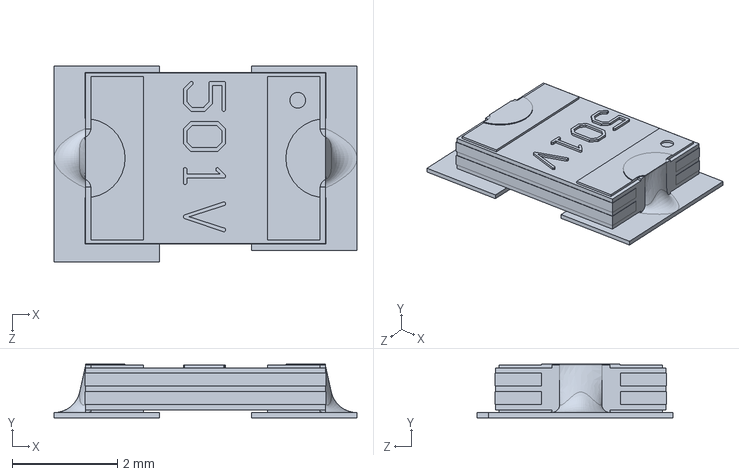
[picture p89: CAD file, 2019-08-14]
CAD/Solidworks/Arduino Uno/mf-msmf050-2.SLDPRT
5.75 x 1.02 x 3.72 mm
