RBinsonB/Nox_robot/CAD/Solidworks/Mounting_bracket_50.SLDPRT

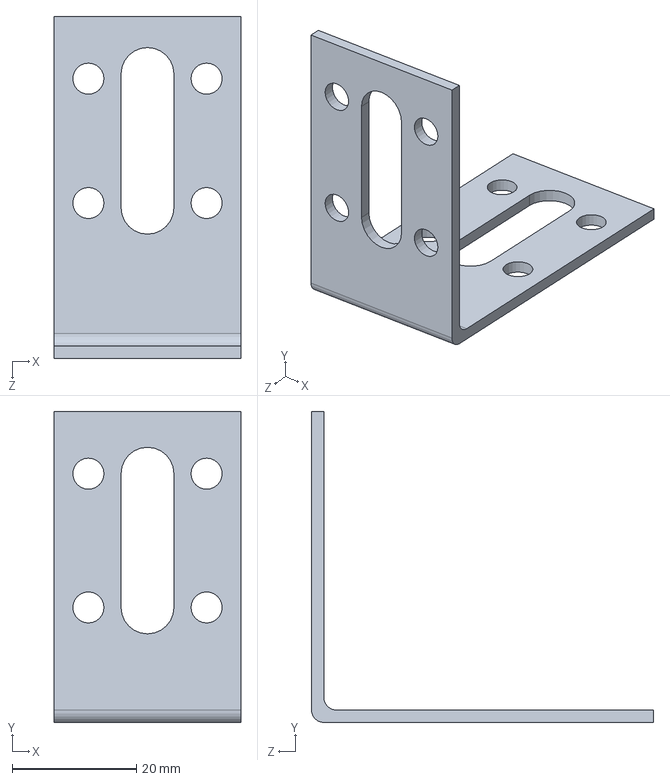
[picture p90: CAD file, 2019-08-14]
CAD/Solidworks/Mounting_bracket_50.SLDPRT
30.0 x 50.0 x 55.0 mm
