RBinsonB/Nox_robot/CAD/Solidworks/Arduino Uno/8 PORT HEADER.SLDPRT

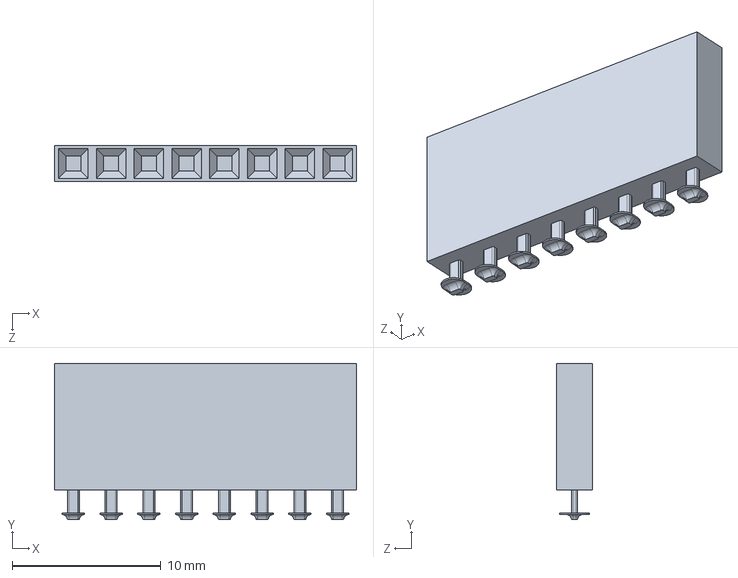
[picture p91: CAD file, 2019-08-14]
CAD/Solidworks/Arduino Uno/8 PORT HEADER.SLDPRT
20.3 x 10.5 x 2.41 mm
