RBinsonB/Nox_robot/CAD/Solidworks/Arduino Uno/lmv358.SLDPRT

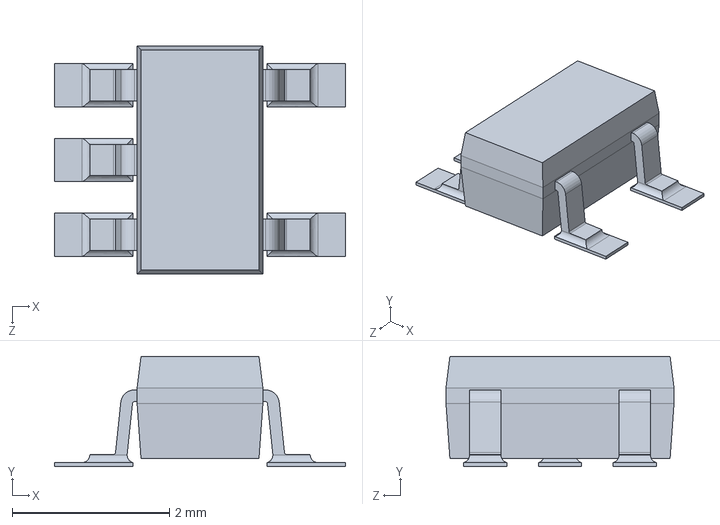
[picture p92: CAD file, 2019-08-14]
CAD/Solidworks/Arduino Uno/lmv358.SLDPRT
3.70 x 1.40 x 2.90 mm
