RBinsonB/Nox_robot/CAD/Solidworks/Arduino Uno/ATMEL328P.SLDPRT

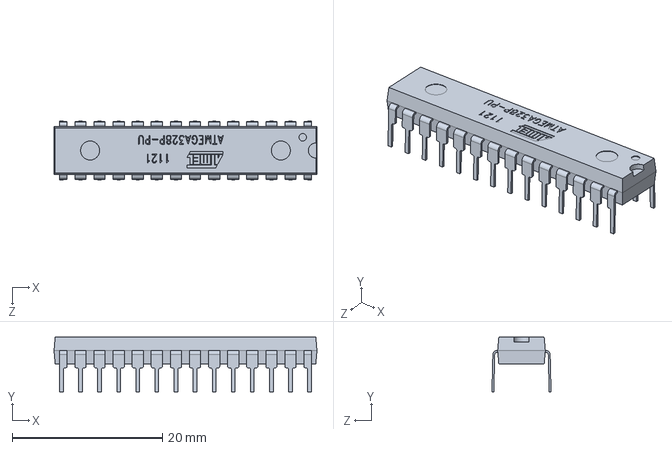
[picture p93: CAD file, 2019-08-14]
CAD/Solidworks/Arduino Uno/ATMEL328P.SLDPRT
35.0 x 7.27 x 7.87 mm
