RBinsonB/Nox_robot/CAD/Solidworks/Arduino Uno/m7 diode.SLDPRT

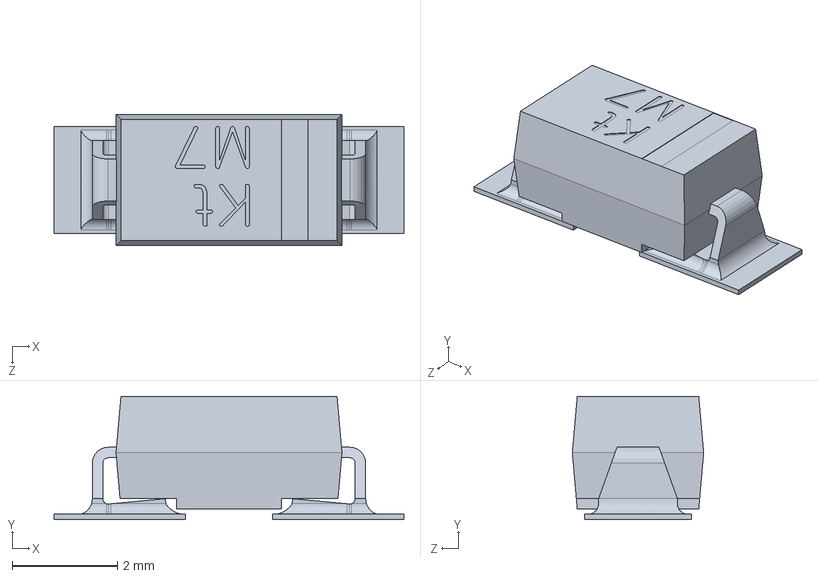
[picture p94: CAD file, 2019-08-14]
CAD/Solidworks/Arduino Uno/m7 diode.SLDPRT
6.66 x 2.35 x 2.50 mm
