RBinsonB/Nox_robot/CAD/Solidworks/Arduino Uno/lp2985dgkr.SLDPRT

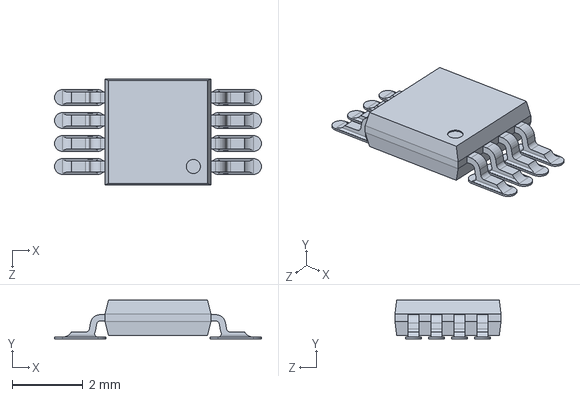
[picture p95: CAD file, 2019-08-14]
CAD/Solidworks/Arduino Uno/lp2985dgkr.SLDPRT
5.85 x 1.10 x 3.00 mm
