RBinsonB/Nox_robot/CAD/Solidworks/Arduino Uno/led.SLDPRT

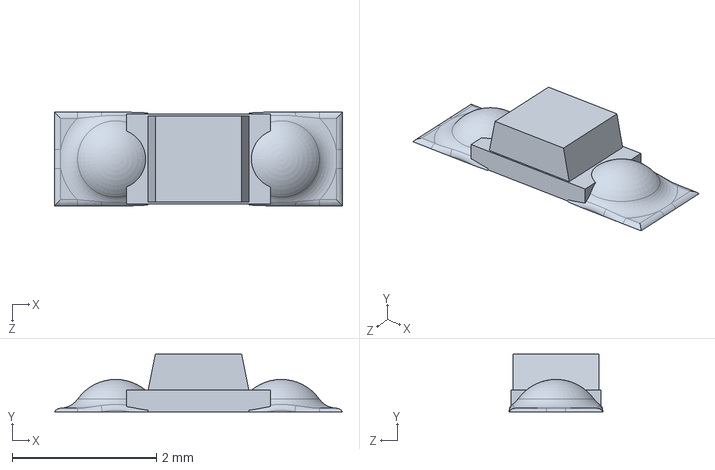
[picture p96: CAD file, 2019-08-14]
CAD/Solidworks/Arduino Uno/led.SLDPRT
4.00 x 0.8 x 1.30 mm
