RBinsonB/Nox_robot/CAD/Solidworks/Arduino Uno/47uf CAP Dcase.SLDPRT

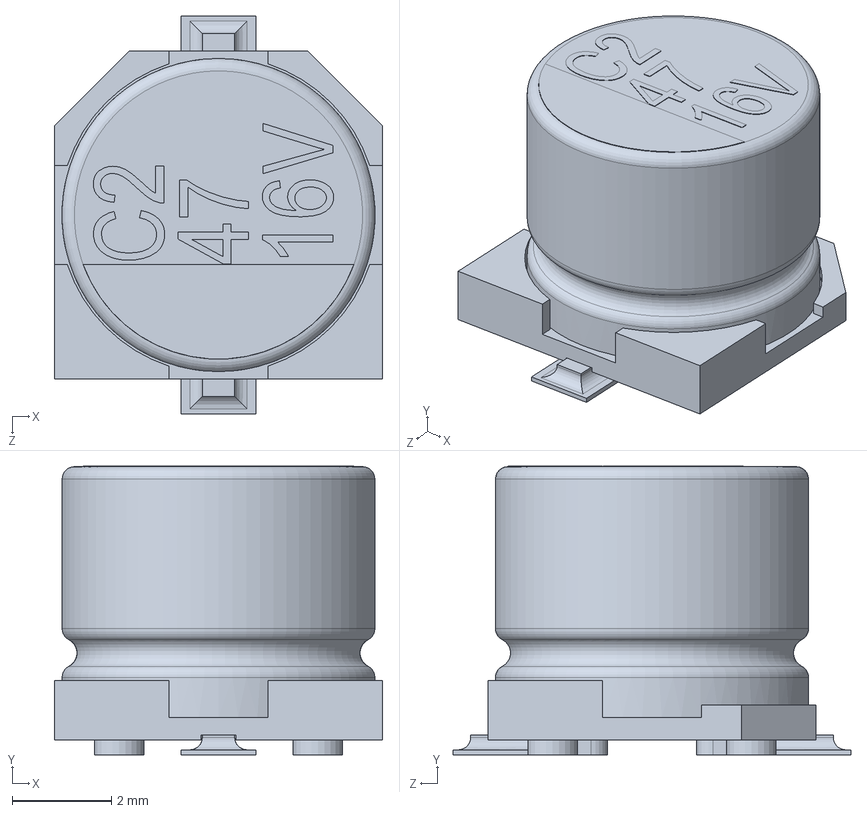
[picture p97: CAD file, 2019-08-14]
CAD/Solidworks/Arduino Uno/47uf CAP Dcase.SLDPRT
6.60 x 5.81 x 8.00 mm
