RBinsonB/Nox_robot/CAD/Solidworks/Arduino Uno/crystal.sldprt

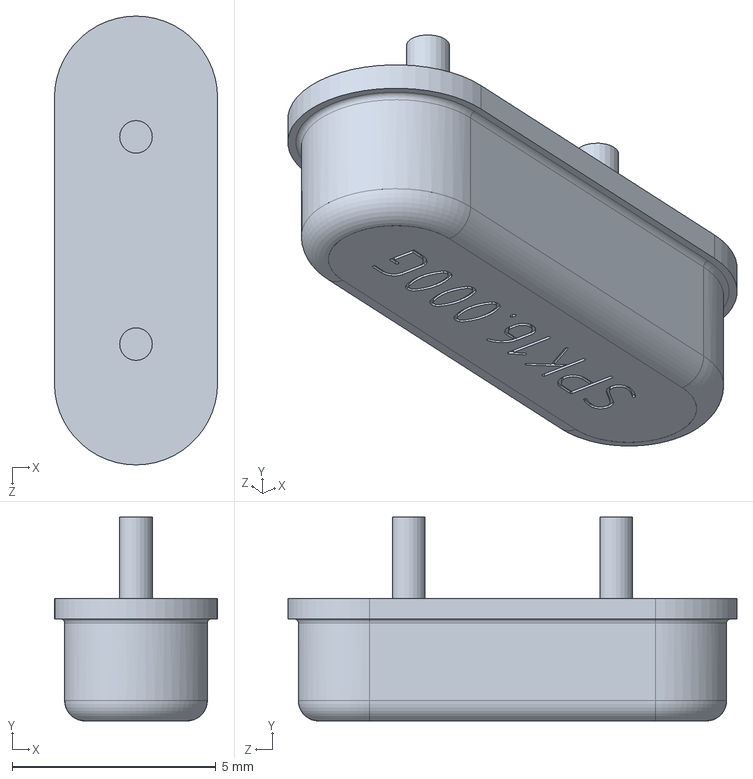
[picture p98: CAD file, 2019-08-14]
CAD/Solidworks/Arduino Uno/crystal.sldprt
4.00 x 5.00 x 11.0 mm
