RBinsonB/Nox_robot/CAD/Solidworks/Arduino Uno/atmega16u2.SLDPRT

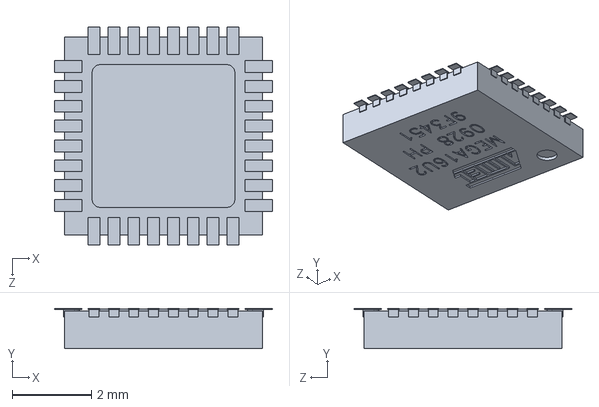
[picture p99: CAD file, 2019-08-14]
CAD/Solidworks/Arduino Uno/atmega16u2.SLDPRT
5.50 x 1.01 x 5.50 mm
