RBinsonB/Nox_robot/CAD/Solidworks/Arduino Uno/603 resistor.SLDPRT

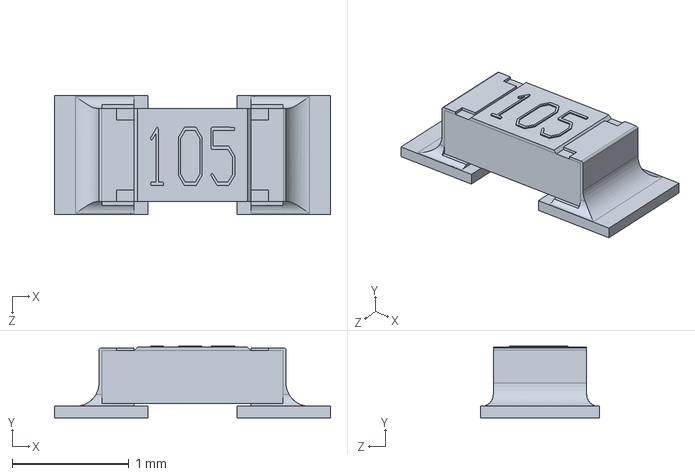
[picture p100: CAD file, 2019-08-14]
CAD/Solidworks/Arduino Uno/603 resistor.SLDPRT
2.36 x 0.615 x 1.02 mm
