RBinsonB/Nox_robot/CAD/Solidworks/Arduino Uno/2pin_header__02.sldprt

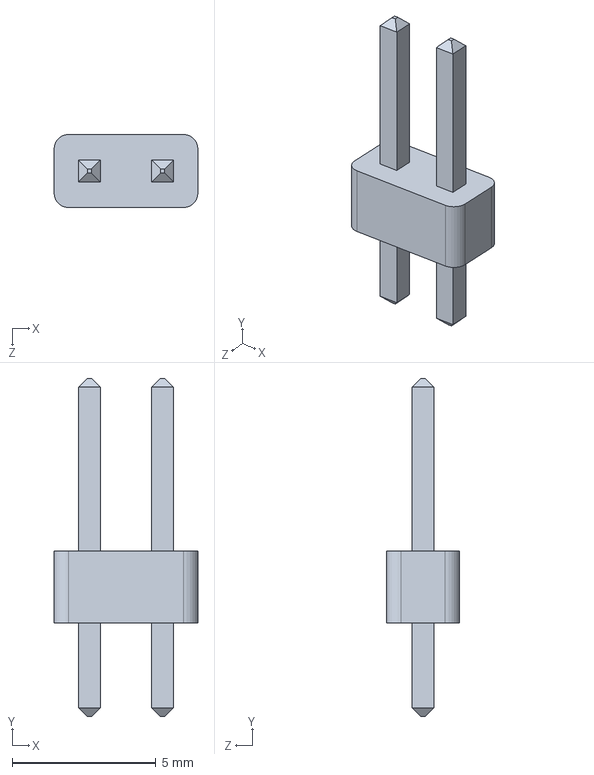
[picture p101: CAD file, 2019-08-14]
CAD/Solidworks/Arduino Uno/2pin_header__02.sldprt
5.00 x 11.8 x 2.54 mm
